4ms/STS/hardware/Kicad-6-project/TrigSampler.kicad_sch

## KiCad design hardware/Kicad-6-project/TrigSampler.kicad_sch (2021-11-30)

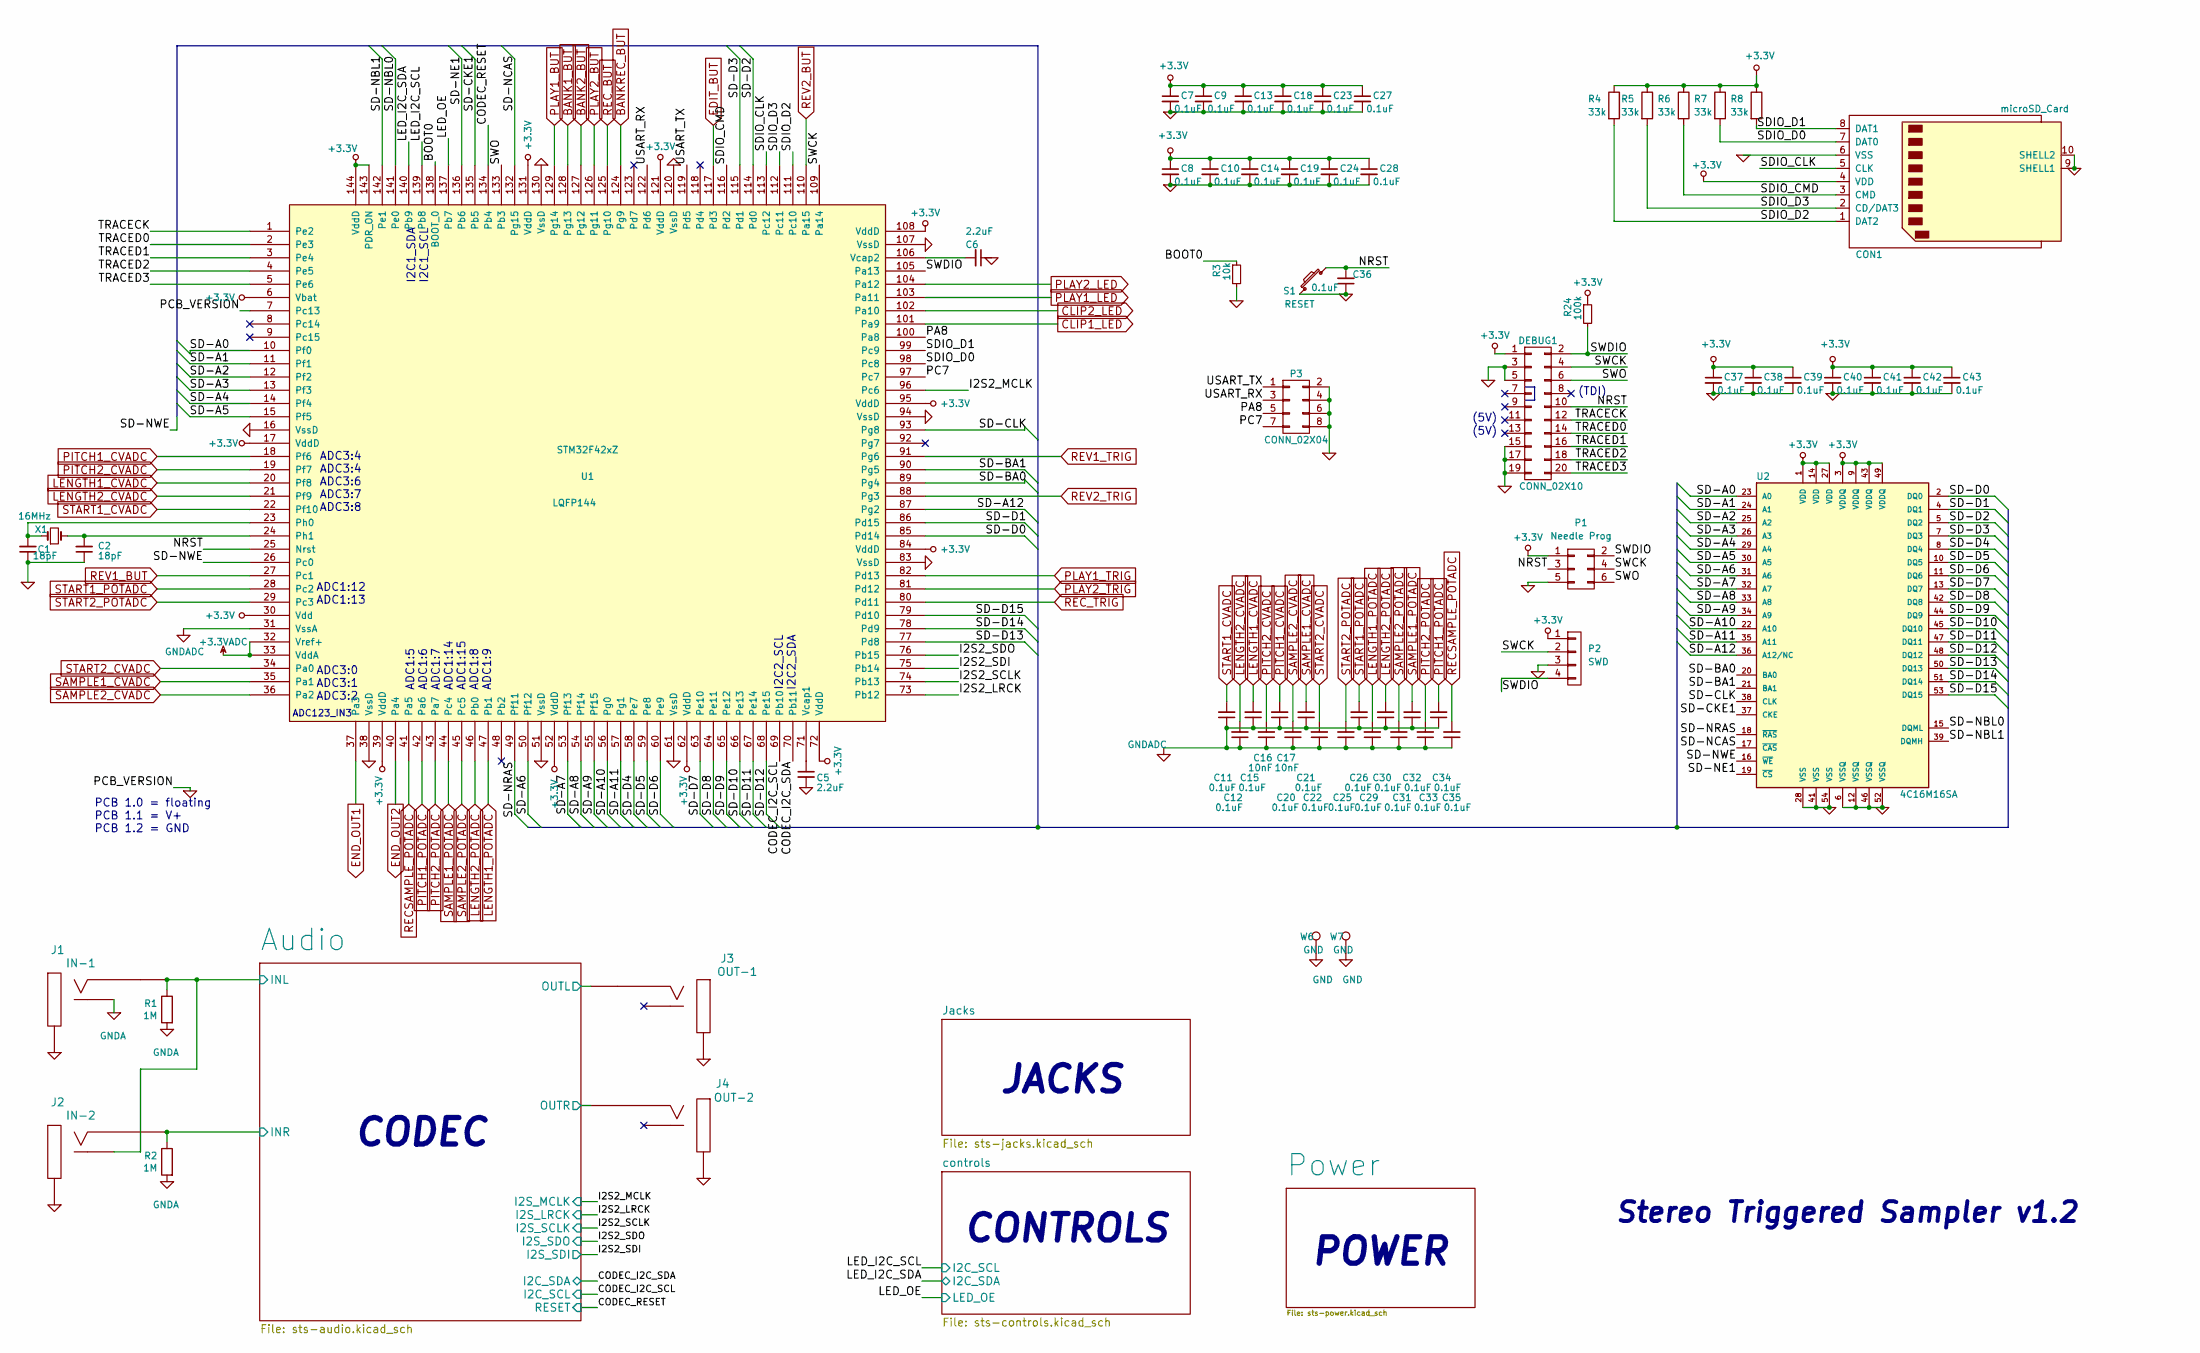
[picture p6: schematic TrigSampler.kicad_sch]

Parts:
C1, C2: 18pF; C0603
C5, C6: 2.2uF; C0603
C7, C8, C9, C10, C11, C12, C13, C14, C15, C18, C19, C20, C21, C22, C23, C24, C25, C26, C27, C28, C29, C30, C31, C32, C33, C34, C35, C36, C37, C38, C39, C40, C41, C42, C43: 0.1uF; C0603
C16, C17: 10nF; C0603
CON1: microSD_Card; MICROSD-YAMAICHI-PJS-VERT
DEBUG1: CONN_02X10; CONN-2x10-SMT-127
J1: IN-1; PJ301M-12
J2: IN-2; PJ301M-12
J3: OUT-1; PJ301M-12
J4: OUT-2; PJ301M-12
P1: Needle Prog; J-LINK_6PIN_NEEDLE_ADAPTER
P2: SWD; Pin_Header_Straight_1x04_Pitch2.54mm
P3: CONN_02X04; Pin_Header_Straight_2x04
R1, R2: 1M; R0603
R3: 10k; R0603
R4, R5, R6, R7, R8: 33k; R0603
R24: 100k; R0603
S1: RESET; BUTTON-TACT-PTS540
U1: STM32F42xZ; LQFP-144_20x20mm_Pitch0.5mm
U2: 4C16M16SA; TSOP-54_W400
W6, W7: GND; TestPoint_Pad_10
X1: 16MHz; FA-238

Connections:
+3.3V: C7.1, C8.1, C9.1, C10.1, C13.1, C14.1, C18.1, C19.1, C23.1, C24.1, C27.1, C28.1, C37.1, C38.1, C39.1, C40.1, C41.1, C42.1, C43.1, CON1.4 (VDD), DEBUG1.1, P1.1, P2.1, R4.1, R5.1, R6.1, R7.1, R8.1, R24.1, U1.6 (Vbat), U1.17 (VddD), U1.30 (Vdd), U1.39 (VddD), U1.52 (VddD), U1.62 (VddD), U1.72 (VddD), U1.84 (VddD), U1.95 (VddD), U1.108 (VddD), U1.121 (VddD), U1.131 (VddD), U1.143 (PDR_ON), U1.144 (VddD), U2.1 (VDD), U2.3 (VDDQ), U2.9 (VDDQ), U2.14 (VDD), U2.27 (VDD), U2.43 (VDDQ), U2.49 (VDDQ)
+3.3VADC: U1.32 (Vref+), U1.33 (VddA)
BANK1_BUT: U1.128 (Pg13)
BANK2_BUT: U1.127 (Pg12)
BANKREC_BUT: U1.124 (Pg9)
BOOT0: R3.1, U1.138 (BOOT_0)
CLIP1_LED: U1.101 (Pa9)
CLIP2_LED: U1.102 (Pa10)
CODEC_I2C_SCL: U1.69 (Pb10)
CODEC_I2C_SDA: U1.70 (Pb11)
CODEC_RESET: U1.134 (Pb4)
EDIT_BUT: U1.117 (Pd3)
END_OUT1: U1.37 (Pa3)
END_OUT2: U1.40 (Pa4)
GND: C1.1, C2.1, C5.2, C6.1, C7.2, C8.2, C9.2, C10.2, C13.2, C14.2, C18.2, C19.2, C23.2, C24.2, C27.2, C28.2, C36.1, C37.2, C38.2, C39.2, C40.2, C41.2, C42.2, C43.2, CON1.6 (VSS), CON1.9 (SHELL1), CON1.10 (SHELL2), DEBUG1.3, DEBUG1.5, DEBUG1.15, DEBUG1.17, DEBUG1.19, J1.2 (SHEILD), J2.2 (SHEILD), J3.2 (SHEILD), J4.2 (SHEILD), P1.5, P2.3, P3.2, P3.4, P3.6, P3.8, R3.2, S1.1, U1.7 (Pc13), U1.16 (VssD), U1.38 (VssD), U1.51 (VssD), U1.61 (VssD), U1.83 (VssD), U1.94 (VssD), U1.107 (VssD), U1.120 (VssD), U1.130 (VssD), U2.6 (VSSQ), U2.12 (VSSQ), U2.28 (VSS), U2.41 (VSS), U2.46 (VSSQ), U2.52 (VSSQ), U2.54 (VSS), W6.1, W7.1
GNDA: J1.3 (SW), R1.2, R2.2
GNDADC: C11.1, C12.1, C15.1, C16.1, C17.1, C20.1, C21.1, C22.1, C25.1, C26.1, C29.1, C30.1, C31.1, C32.1, C33.1, C34.1, C35.1, U1.31 (VssA)
I2S2_LRCK: U1.73 (Pb12)
I2S2_MCLK: U1.96 (Pc6)
I2S2_SCLK: U1.74 (Pb13)
I2S2_SDI: U1.75 (Pb14)
I2S2_SDO: U1.76 (Pb15)
INL: J1.1 (SIG), J2.3 (SW), R1.1
INR: J2.1 (SIG), R2.1
LED_I2C_SCL: U1.139 (Pb8)
LED_I2C_SDA: U1.140 (Pb9)
LED_OE: U1.137 (Pb7)
LENGTH1_CVADC: C15.2, U1.20 (Pf8)
LENGTH1_POTADC: C29.2, U1.47 (Pb1)
LENGTH2_CVADC: C12.2, U1.21 (Pf9)
LENGTH2_POTADC: C30.2, U1.46 (Pb0)
NRST: C36.2, DEBUG1.10, P1.3, S1.2, U1.25 (Nrst)
unnamed: C1.2, U1.23 (Ph0), X1.1
unnamed: C2.2, U1.24 (Ph1), X1.2
unnamed: C5.1, U1.71 (Vcap1)
unnamed: C6.2, U1.106 (Vcap2)
OUTL: J3.1 (SIG)
OUTR: J4.1 (SIG)
PA8: P3.5, U1.100 (Pa8)
PC7: P3.7, U1.97 (Pc7)
PITCH1_CVADC: C17.2, U1.18 (Pf6)
PITCH1_POTADC: C34.2, U1.42 (Pa6)
PITCH2_CVADC: C16.2, U1.19 (Pf7)
PITCH2_POTADC: C33.2, U1.43 (Pa7)
PLAY1_BUT: U1.129 (Pg14)
PLAY1_LED: U1.103 (Pa11)
PLAY1_TRIG: U1.82 (Pd13)
PLAY2_BUT: U1.126 (Pg11)
PLAY2_LED: U1.104 (Pa12)
PLAY2_TRIG: U1.81 (Pd12)
RECSAMPLE_POTADC: C35.2, U1.41 (Pa5)
REC_BUT: U1.125 (Pg10)
REC_TRIG: U1.80 (Pd11)
REV1_BUT: U1.27 (Pc1)
REV1_TRIG: U1.91 (Pg6)
REV2_BUT: U1.110 (Pa15)
REV2_TRIG: U1.88 (Pg3)
SAMPLE1_CVADC: C21.2, U1.35 (Pa1)
SAMPLE1_POTADC: C32.2, U1.44 (Pc4)
SAMPLE2_CVADC: C20.2, U1.36 (Pa2)
SAMPLE2_POTADC: C31.2, U1.45 (Pc5)
SD-A0: U1.10 (Pf0), U2.23 (A0)
SD-A1: U1.11 (Pf1), U2.24 (A1)
SD-A2: U1.12 (Pf2), U2.25 (A2)
SD-A3: U1.13 (Pf3), U2.26 (A3)
SD-A4: U1.14 (Pf4), U2.29 (A4)
SD-A5: U1.15 (Pf5), U2.30 (A5)
SD-A6: U1.50 (Pf12), U2.31 (A6)
SD-A7: U1.53 (Pf13), U2.32 (A7)
SD-A8: U1.54 (Pf14), U2.33 (A8)
SD-A9: U1.55 (Pf15), U2.34 (A9)
SD-A10: U1.56 (Pg0), U2.22 (A10)
SD-A11: U1.57 (Pg1), U2.35 (A11)
SD-A12: U1.87 (Pg2), U2.36 (A12/NC)
SD-BA0: U1.89 (Pg4), U2.20 (BA0)
SD-BA1: U1.90 (Pg5), U2.21 (BA1)
SD-CKE1: U1.135 (Pb5), U2.37 (CKE)
SD-CLK: U1.93 (Pg8), U2.38 (CLK)
SD-D0: U1.85 (Pd14), U2.2 (DQ0)
SD-D1: U1.86 (Pd15), U2.4 (DQ1)
SD-D2: U1.114 (Pd0), U2.5 (DQ2)
SD-D3: U1.115 (Pd1), U2.7 (DQ3)
SD-D4: U1.58 (Pe7), U2.8 (DQ4)
SD-D5: U1.59 (Pe8), U2.10 (DQ5)
SD-D6: U1.60 (Pe9), U2.11 (DQ6)
SD-D7: U1.63 (Pe10), U2.13 (DQ7)
SD-D8: U1.64 (Pe11), U2.42 (DQ8)
SD-D9: U1.65 (Pe12), U2.44 (DQ9)
SD-D10: U1.66 (Pe13), U2.45 (DQ10)
SD-D11: U1.67 (Pe14), U2.47 (DQ11)
SD-D12: U1.68 (Pe15), U2.48 (DQ12)
SD-D13: U1.77 (Pd8), U2.50 (DQ13)
SD-D14: U1.78 (Pd9), U2.51 (DQ14)
SD-D15: U1.79 (Pd10), U2.53 (DQ15)
SD-NBL0: U1.141 (Pe0), U2.15 (DQML)
SD-NBL1: U1.142 (Pe1), U2.39 (DQMH)
SD-NCAS: U1.132 (Pg15), U2.17 (~CAS)
SD-NE1: U1.136 (Pb6), U2.19 (~CS)
SD-NRAS: U1.49 (Pf11), U2.18 (~RAS)
SD-NWE: U1.26 (Pc0), U2.16 (~WE)
SDIO_CLK: CON1.5 (CLK), U1.113 (Pc12)
SDIO_CMD: CON1.3 (CMD), R6.2, U1.116 (Pd2)
SDIO_D0: CON1.7 (DAT0), R7.2, U1.98 (Pc8)
SDIO_D1: CON1.8 (DAT1), R8.2, U1.99 (Pc9)
SDIO_D2: CON1.1 (DAT2), R4.2, U1.111 (Pc10)
SDIO_D3: CON1.2 (CD/DAT3), R5.2, U1.112 (Pc11)
START1_CVADC: C11.2, U1.22 (Pf10)
START1_POTADC: C26.2, U1.28 (Pc2)
START2_CVADC: C22.2, U1.34 (Pa0)
START2_POTADC: C25.2, U1.29 (Pc3)
SWCK: DEBUG1.4, P1.4, P2.2, U1.109 (Pa14)
SWDIO: DEBUG1.2, P1.2, P2.4, R24.2, U1.105 (Pa13)
SWO: DEBUG1.6, P1.6, U1.133 (Pb3)
TRACECK: DEBUG1.12, U1.1 (Pe2)
TRACED0: DEBUG1.14, U1.2 (Pe3)
TRACED1: DEBUG1.16, U1.3 (Pe4)
TRACED2: DEBUG1.18, U1.4 (Pe5)
TRACED3: DEBUG1.20, U1.5 (Pe6)
USART_RX: P3.3, U1.122 (Pd6)
USART_TX: P3.1, U1.119 (Pd5)

Notes on the sheet:
JACKS
PCB 1.0 = floating PCB 1.1 = V+ PCB 1.2 = GND
(5V)
ADC3:4 ADC3:4 ADC3:6 ADC3:7 ADC3:8
ADC123_IN3
ADC1:5 ADC1:6 ADC1:7 ADC1:14 ADC1:15 ADC1:8 ADC1:9
ADC1:12 ADC1:13
POWER
I2C1_SDA I2C1_SCL
(TDI)
I2C2_SCL I2C2_SDA
Stereo Triggered Sampler v1.2
CONTROLS
CODEC
ADC3:0 ADC3:1 ADC3:2
