4ms/STS/hardware/Kicad-6-project/sts-audio.kicad_sch

## KiCad design hardware/Kicad-6-project/sts-audio.kicad_sch (2021-11-30)

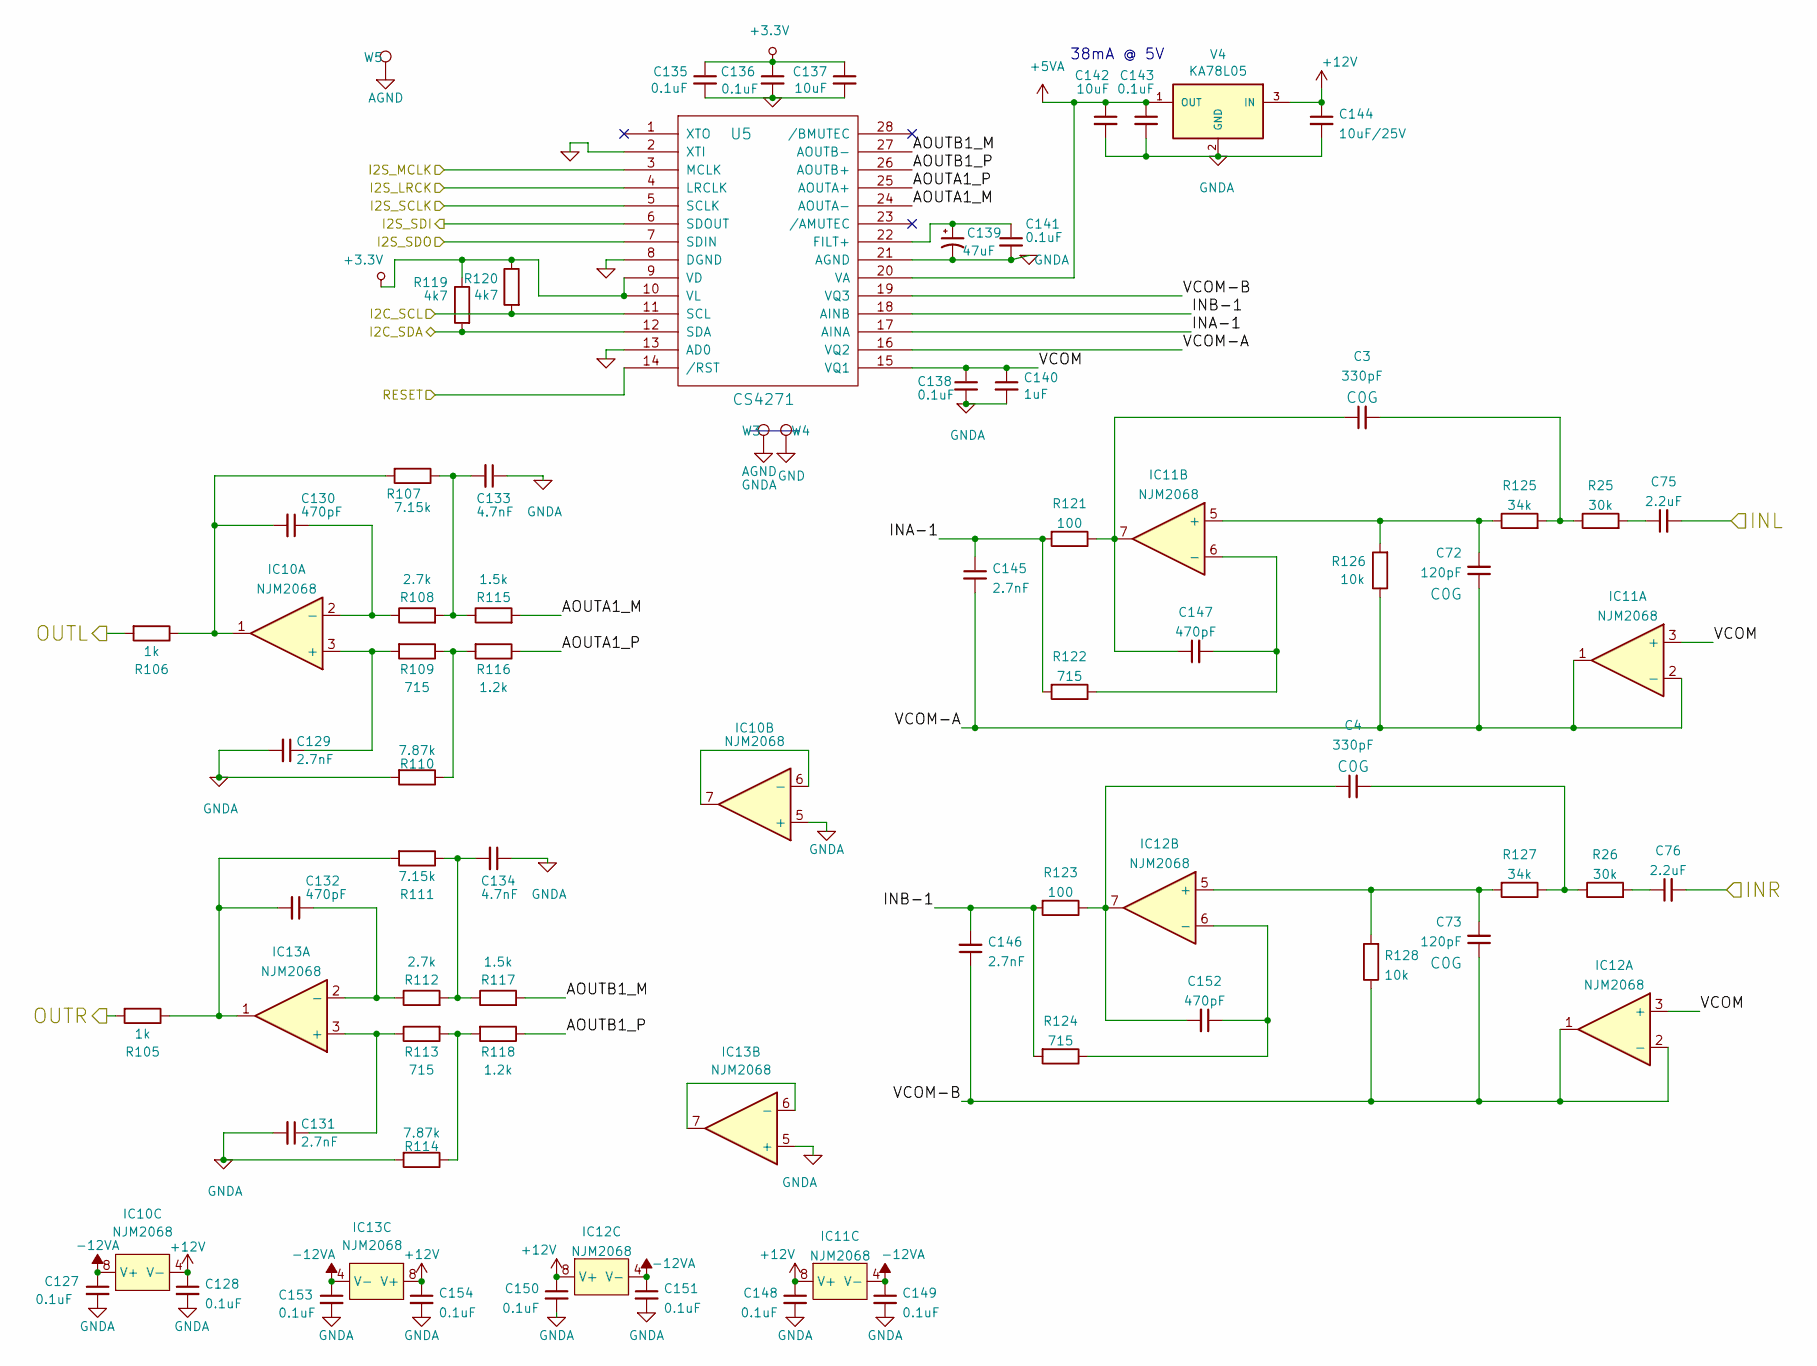
[picture p7: schematic sts-audio.kicad_sch]

Parts:
C3, C4: 330pF; C0603; Tolerance 1%
C72, C73: 120pF; C0603; Tolerance 1%
C75, C76: 2.2uF; C0603
C127, C128, C135, C136, C138, C141, C143, C148, C149, C150, C151, C153, C154: 0.1uF; C0603
C129, C131, C145, C146: 2.7nF; C0603
C130, C132, C147, C152: 470pF; C0603
C133, C134: 4.7nF; C0603
C137, C142: 10uF; C0603
C139: 47uF; c_elec_5x5.3
C140: 1uF; C0603
C144: 10uF/25V; C1206
IC10, IC11, IC12, IC13: NJM2068; TSSOP-8_4.4x3mm_Pitch0.65mm; Part Number NJM2068V-TE1
R25, R26: 30k; R0603
R105, R106: 1k; R0603
R107, R111: 7.15k; R0603
R108, R112: 2.7k; R0603
R109, R113, R122, R124: 715; R0603
R110, R114: 7.87k; R0603
R115, R117: 1.5k; R0603
R116, R118: 1.2k; R0603
R119, R120: 4k7; R0603
R121, R123: 100; R0603
R125, R127: 34k; R0603
R126, R128: 10k; R0603
U5: CS4271; TSSOP-28_4.4x9.7mm_Pitch0.65mm
V4: KA78L05; SOT89-3_Housing
W3, W5: AGND; PAD-06
W4: GND; PAD-06

Connections:
+3.3V: C135.1, C136.1, C137.1, R119.1, R120.1, U5.9 (VD), U5.10 (VL)
+5VA: C142.1, C143.1, U5.20 (VA), V4.1 (OUT)
+12V: C128.1, C144.1, C148.1, C150.1, C154.1, IC10.4 (V-), IC11.8 (V+), IC12.8 (V+), IC13.8 (V+), V4.3 (IN)
-12VA: C127.1, C149.1, C151.1, C153.1, IC10.8 (V+), IC11.4 (V-), IC12.4 (V-), IC13.4 (V-)
AOUTA1_M: R115.2, U5.24 (AOUTA-)
AOUTA1_P: R116.1, U5.25 (AOUTA+)
AOUTB1_M: R117.2, U5.27 (AOUTB-)
AOUTB1_P: R118.1, U5.26 (AOUTB+)
GND: C135.2, C136.2, C137.2, U5.2 (XTI), U5.8 (DGND), U5.13 (AD0), W4.1, W5.1
GNDA: C127.2, C128.2, C129.2, C131.2, C133.1, C134.1, C138.2, C139.2, C140.2, C141.2, C142.2, C143.2, C144.2, C148.2, C149.2, C150.2, C151.2, C153.2, C154.2, IC10.5 (+), IC13.5 (+), R110.2, R114.2, U5.21 (AGND), V4.2 (GND), W3.1
I2C_SCL: R120.2, U5.11 (SCL)
I2C_SDA: R119.2, U5.12 (SDA)
I2S_LRCK: U5.4 (LRCLK)
I2S_MCLK: U5.3 (MCLK)
I2S_SCLK: U5.5 (SCLK)
I2S_SDI: U5.6 (SDOUT)
I2S_SDO: U5.7 (SDIN)
INA-1: C145.1, R121.2, R122.2, U5.17 (AINA)
INB-1: C146.2, R123.2, R124.2, U5.18 (AINB)
INL: C75.2
INR: C76.2
unnamed: C3.2, R25.1, R125.2
unnamed: C4.2, R26.1, R127.1
unnamed: C72.2, IC11.5 (+), R125.1, R126.2
unnamed: C73.2, IC12.5 (+), R127.2, R128.2
unnamed: C75.1, R25.2
unnamed: C76.1, R26.2
unnamed: C129.1, IC10.3 (+), R109.2
unnamed: C130.1, IC10.2 (-), R108.1
unnamed: C130.2, IC10.1, R106.1, R107.2
unnamed: C131.1, IC13.3 (+), R113.1
unnamed: C132.1, IC13.2 (-), R112.1
unnamed: C132.2, IC13.1, R105.1, R111.2
unnamed: C133.2, R107.1, R108.2, R115.1
unnamed: C134.2, R111.1, R112.2, R117.1
unnamed: C139.1, C141.1, U5.22 (FILT+)
unnamed: C3.1, C147.1, IC11.7, R121.1
unnamed: C147.2, IC11.6 (-), R122.1
unnamed: C152.1, IC12.6 (-), R124.1
unnamed: C4.1, C152.2, IC12.7, R123.1
unnamed: IC10.6 (-), IC10.7
unnamed: IC13.6 (-), IC13.7
unnamed: R109.1, R110.1, R116.2
unnamed: R113.2, R114.1, R118.2
OUTL: R106.2
OUTR: R105.2
RESET: U5.14 (/RST)
VCOM: C138.1, C140.1, IC11.3 (+), IC12.3 (+), U5.15 (VQ1)
VCOM-A: C72.1, C145.2, IC11.1, IC11.2 (-), R126.1, U5.16 (VQ2)
VCOM-B: C73.1, C146.1, IC12.1, IC12.2 (-), R128.1, U5.19 (VQ3)

Notes on the sheet:
38mA @ 5V
