4ms/STS/hardware/Kicad-6-project/sts-controls.kicad_sch

## KiCad design hardware/Kicad-6-project/sts-controls.kicad_sch (2021-11-30)

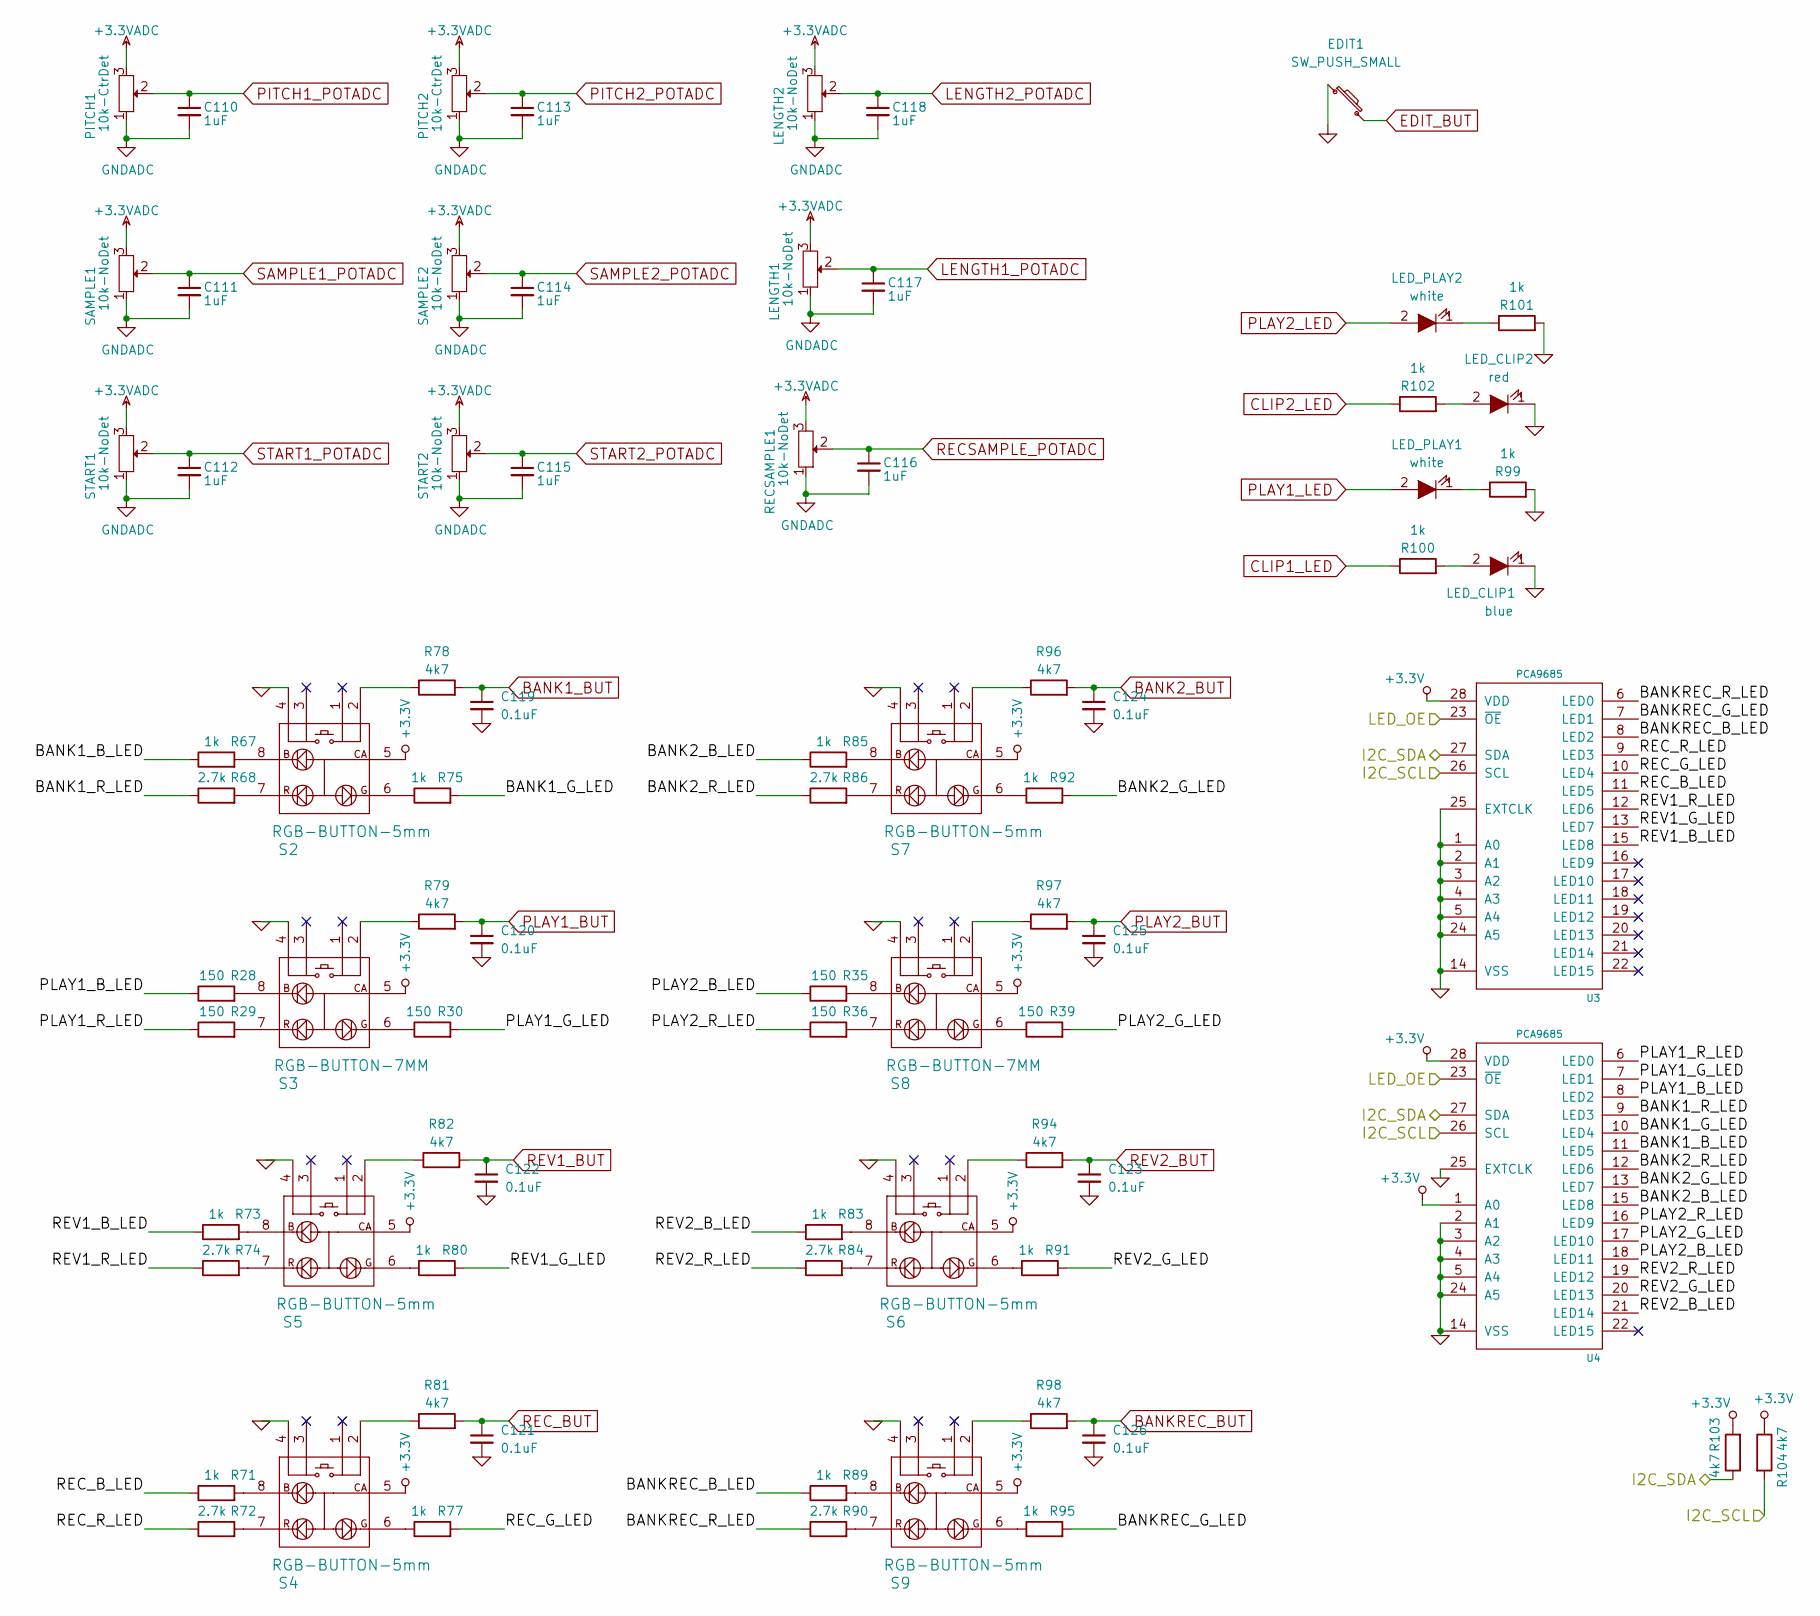
[picture p8: schematic sts-controls.kicad_sch]

Parts:
C110, C111, C112, C113, C114, C115, C116, C117, C118: 1uF; C0603
C119, C120, C121, C122, C123, C124, C125, C126: 0.1uF; C0603
EDIT1: SW_PUSH_SMALL; SPST-SUB
LED_CLIP1: blue; LED-3MM-SQUARE-ANODE
LED_CLIP2: red; LED-3MM-SQUARE-ANODE
LED_PLAY1, LED_PLAY2: white; LED-3MM-SQUARE-ANODE
LENGTH1, LENGTH2: 10k-NoDet; 16MM-RV16AF-4A-NODET
PITCH1, PITCH2: 10k-CtrDet; 16MM-RV16AF-4A-CTRDET
R28, R29, R30, R35, R36, R39: 150; R0603
R67, R71, R73, R75, R77, R80, R83, R85, R89, R91, R92, R95, R99, R100, R101, R102: 1k; R0603
R68, R72, R74, R84, R86, R90: 2.7k; R0603
R78, R79, R81, R82, R94, R96, R97, R98, R103, R104: 4k7; R0603
RECSAMPLE1: 10k-NoDet; 16MM-RV16AF-4A-NODET
S2, S7: RGB-BUTTON-5mm; Button_RgbLED_SPST_TC002
S3, S8: RGB-BUTTON-7MM; Button_RgbLED_SPST_PB615303HL-7mm
S4, S5, S6, S9: RGB-BUTTON-5mm; RGB-SPST-LED-TC002
SAMPLE1, SAMPLE2: 10k-NoDet; 16MM-RV16AF-4A-NODET
START1, START2: 10k-NoDet; 16MM-RV16AF-4A-NODET
U3, U4: PCA9685; TSSOP-28_4.4x9.7mm_Pitch0.65mm

Connections:
+3.3V: R103.2, R104.1, S2.5 (CA), S3.5 (CA), S4.5 (CA), S5.5 (CA), S6.5 (CA), S7.5 (CA), S8.5 (CA), S9.5 (CA), U3.28 (VDD), U4.1 (A0), U4.28 (VDD)
+3.3VADC: LENGTH1.3, LENGTH2.3, PITCH1.3, PITCH2.3, RECSAMPLE1.3, SAMPLE1.3, SAMPLE2.3, START1.3, START2.3
BANK1_BUT: C119.1, R78.2
BANK1_B_LED: R67.1, U4.11 (LED5)
BANK1_G_LED: R75.2, U4.10 (LED4)
BANK1_R_LED: R68.1, U4.9 (LED3)
BANK2_BUT: C124.1, R96.2
BANK2_B_LED: R85.1, U4.15 (LED8)
BANK2_G_LED: R92.2, U4.13 (LED7)
BANK2_R_LED: R86.1, U4.12 (LED6)
BANKREC_BUT: C126.1, R98.2
BANKREC_B_LED: R89.1, U3.8 (LED2)
BANKREC_G_LED: R95.2, U3.7 (LED1)
BANKREC_R_LED: R90.1, U3.6 (LED0)
CLIP1_LED: R100.1
CLIP2_LED: R102.1
EDIT_BUT: EDIT1.2
GND: C119.2, C120.2, C121.2, C122.2, C123.2, C124.2, C125.2, C126.2, EDIT1.1, LED_CLIP1.1 (K), LED_CLIP2.1 (K), R99.2, R101.2, S2.4 (UP-B), S3.4 (UP-B), S4.4 (UP-B), S5.4 (UP-B), S6.4 (UP-B), S7.4 (UP-B), S8.4 (UP-B), S9.4 (UP-B), U3.1 (A0), U3.2 (A1), U3.3 (A2), U3.4 (A3), U3.5 (A4), U3.14 (VSS), U3.24 (A5), U3.25 (EXTCLK), U4.2 (A1), U4.3 (A2), U4.4 (A3), U4.5 (A4), U4.14 (VSS), U4.24 (A5), U4.25 (EXTCLK)
GNDADC: C110.2, C111.2, C112.2, C113.2, C114.2, C115.2, C116.2, C117.2, C118.2, LENGTH1.1, LENGTH2.1, PITCH1.1, PITCH2.1, RECSAMPLE1.1, SAMPLE1.1, SAMPLE2.1, START1.1, START2.1
I2C_SCL: R104.2, U3.26 (SCL), U4.26 (SCL)
I2C_SDA: R103.1, U3.27 (SDA), U4.27 (SDA)
LED_OE: U3.23 (~OE), U4.23 (~OE)
LENGTH1_POTADC: C117.1, LENGTH1.2
LENGTH2_POTADC: C118.1, LENGTH2.2
unnamed: LED_CLIP1.2 (A), R100.2
unnamed: LED_CLIP2.2 (A), R102.2
unnamed: LED_PLAY1.1 (K), R99.1
unnamed: LED_PLAY2.1 (K), R101.1
unnamed: R28.2, S3.8 (B)
unnamed: R29.2, S3.7 (R)
unnamed: R30.1, S3.6 (G)
unnamed: R35.2, S8.8 (B)
unnamed: R36.2, S8.7 (R)
unnamed: R39.1, S8.6 (G)
unnamed: R67.2, S2.8 (B)
unnamed: R68.2, S2.7 (R)
unnamed: R71.2, S4.8 (B)
unnamed: R72.2, S4.7 (R)
unnamed: R73.2, S5.8 (B)
unnamed: R74.2, S5.7 (R)
unnamed: R75.1, S2.6 (G)
unnamed: R77.1, S4.6 (G)
unnamed: R78.1, S2.2 (POLE-A)
unnamed: R79.1, S3.2 (POLE-A)
unnamed: R80.1, S5.6 (G)
unnamed: R81.1, S4.2 (POLE-A)
unnamed: R82.1, S5.2 (POLE-A)
unnamed: R83.2, S6.8 (B)
unnamed: R84.2, S6.7 (R)
unnamed: R85.2, S7.8 (B)
unnamed: R86.2, S7.7 (R)
unnamed: R89.2, S9.8 (B)
unnamed: R90.2, S9.7 (R)
unnamed: R91.1, S6.6 (G)
unnamed: R92.1, S7.6 (G)
unnamed: R94.1, S6.2 (POLE-A)
unnamed: R95.1, S9.6 (G)
unnamed: R96.1, S7.2 (POLE-A)
unnamed: R97.1, S8.2 (POLE-A)
unnamed: R98.1, S9.2 (POLE-A)
PITCH1_POTADC: C110.1, PITCH1.2
PITCH2_POTADC: C113.1, PITCH2.2
PLAY1_BUT: C120.1, R79.2
PLAY1_B_LED: R28.1, U4.8 (LED2)
PLAY1_G_LED: R30.2, U4.7 (LED1)
PLAY1_LED: LED_PLAY1.2 (A)
PLAY1_R_LED: R29.1, U4.6 (LED0)
PLAY2_BUT: C125.1, R97.2
PLAY2_B_LED: R35.1, U4.18 (LED11)
PLAY2_G_LED: R39.2, U4.17 (LED10)
PLAY2_LED: LED_PLAY2.2 (A)
PLAY2_R_LED: R36.1, U4.16 (LED9)
RECSAMPLE_POTADC: C116.1, RECSAMPLE1.2
REC_BUT: C121.1, R81.2
REC_B_LED: R71.1, U3.11 (LED5)
REC_G_LED: R77.2, U3.10 (LED4)
REC_R_LED: R72.1, U3.9 (LED3)
REV1_BUT: C122.1, R82.2
REV1_B_LED: R73.1, U3.15 (LED8)
REV1_G_LED: R80.2, U3.13 (LED7)
REV1_R_LED: R74.1, U3.12 (LED6)
REV2_BUT: C123.1, R94.2
REV2_B_LED: R83.1, U4.21 (LED14)
REV2_G_LED: R91.2, U4.20 (LED13)
REV2_R_LED: R84.1, U4.19 (LED12)
SAMPLE1_POTADC: C111.1, SAMPLE1.2
SAMPLE2_POTADC: C114.1, SAMPLE2.2
START1_POTADC: C112.1, START1.2
START2_POTADC: C115.1, START2.2
