4ms/STS/hardware/Kicad-6-project/sts-jacks.kicad_sch

## KiCad design hardware/Kicad-6-project/sts-jacks.kicad_sch (2021-11-30)

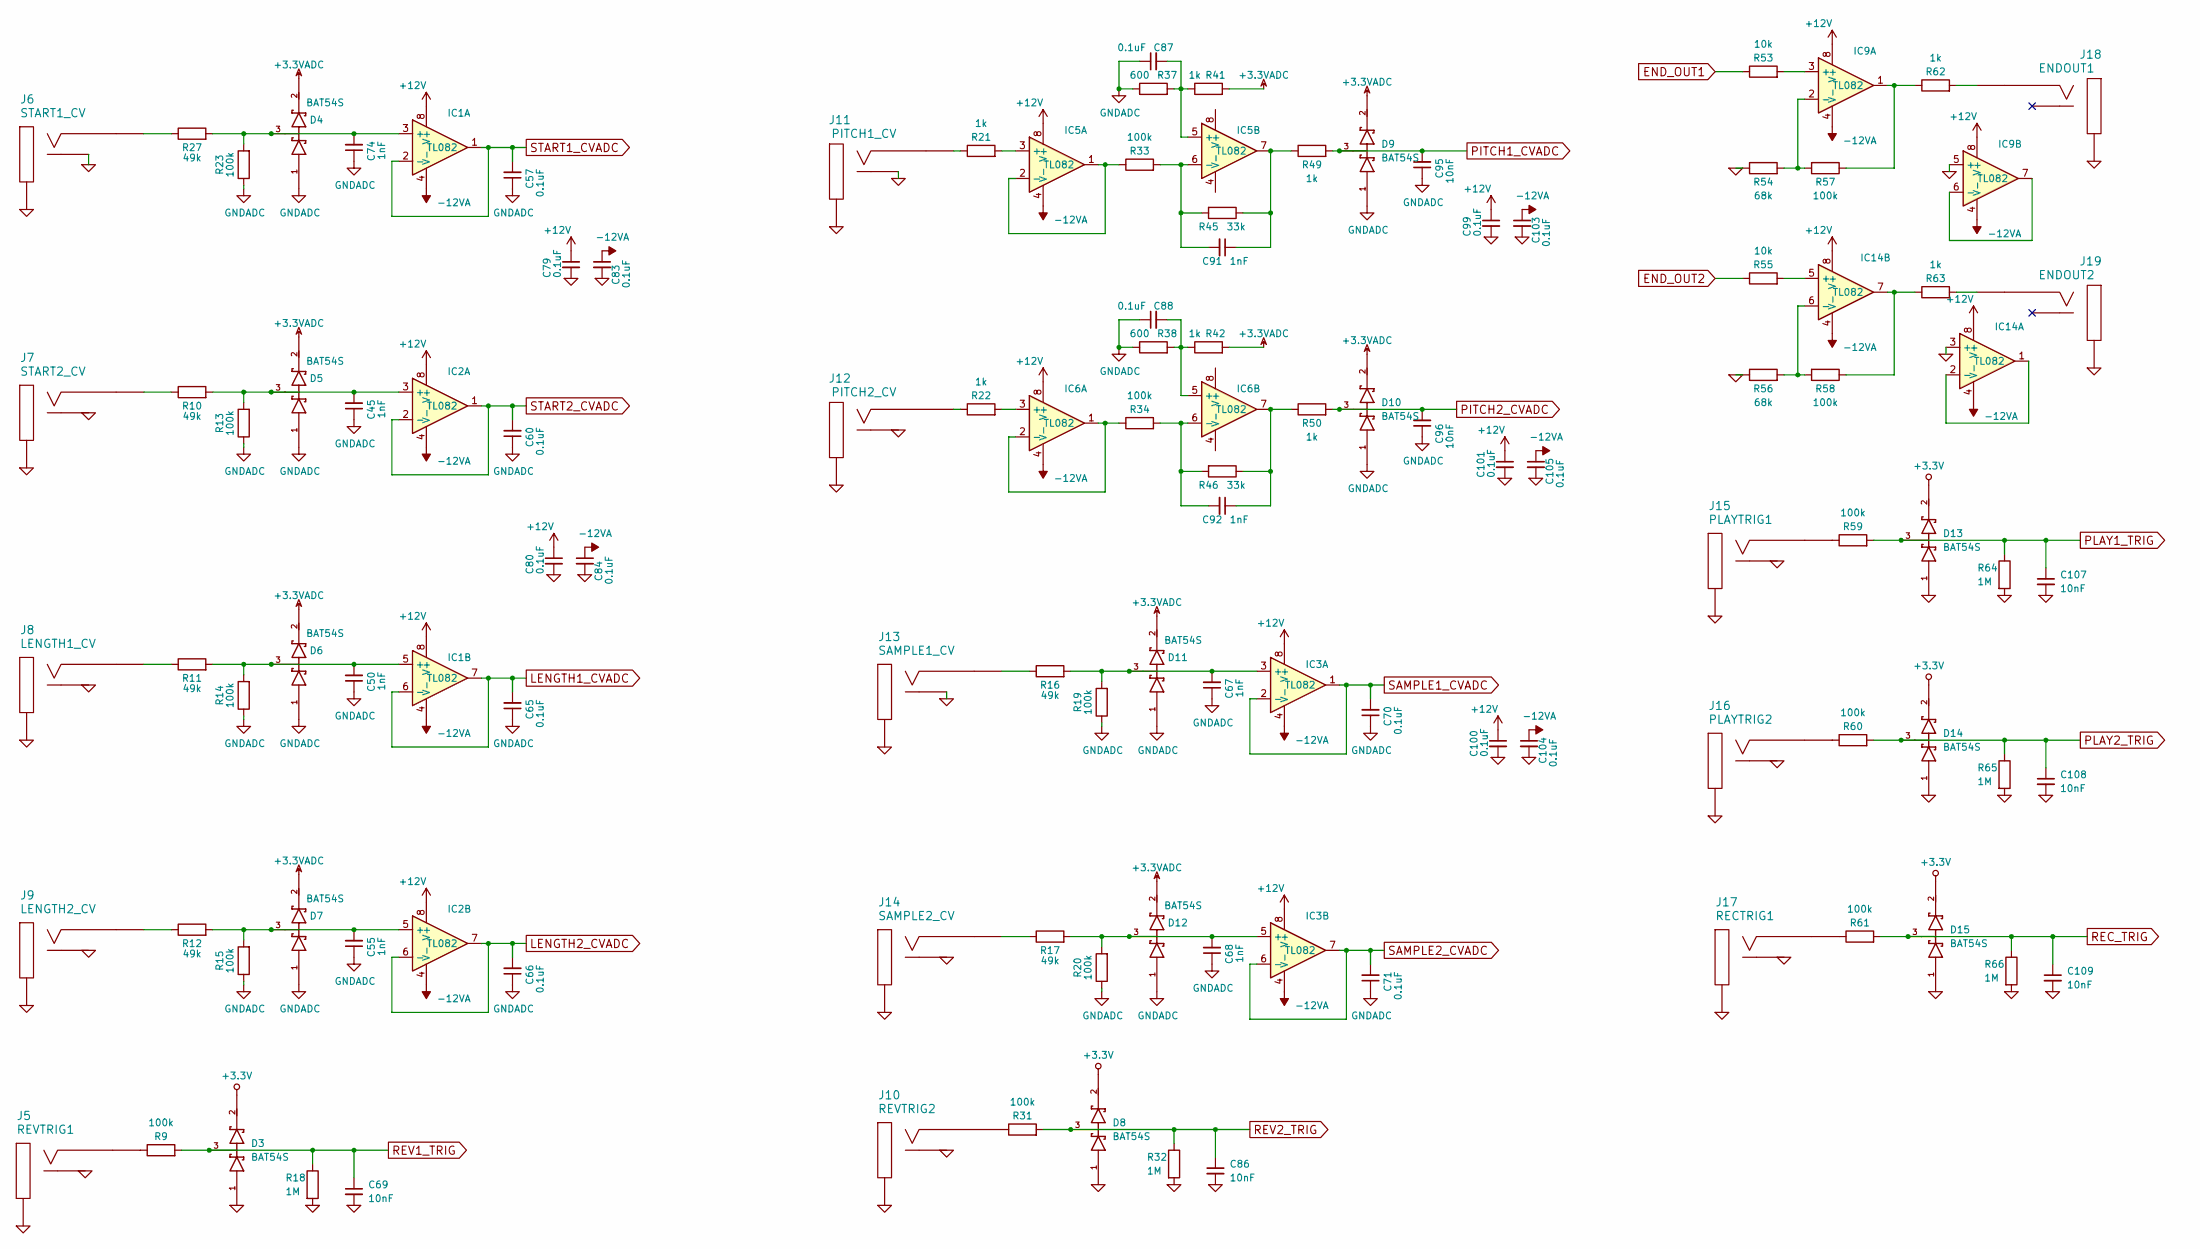
[picture p9: schematic sts-jacks.kicad_sch]

Parts:
C45, C50, C55, C67, C68, C74, C91, C92: 1nF; C0603
C57, C60, C65, C66, C70, C71, C79, C80, C83, C84, C87, C88, C99, C100, C101, C103, C104, C105: 0.1uF; C0603
C69, C86, C95, C96, C107, C108, C109: 10nF; C0603
D3, D4, D5, D6, D7, D8, D9, D10, D11, D12, D13, D14, D15: BAT54S; SOT23
IC1, IC2, IC3, IC5, IC6, IC9, IC14: TL082; TSSOP-8_4.4x3mm_Pitch0.65mm
J5: REVTRIG1; PJ301M-12
J6: START1_CV; PJ301M-12
J7: START2_CV; PJ301M-12
J8: LENGTH1_CV; PJ301M-12
J9: LENGTH2_CV; PJ301M-12
J10: REVTRIG2; PJ301M-12
J11: PITCH1_CV; PJ301M-12
J12: PITCH2_CV; PJ301M-12
J13: SAMPLE1_CV; PJ301M-12
J14: SAMPLE2_CV; PJ301M-12
J15: PLAYTRIG1; PJ301M-12
J16: PLAYTRIG2; PJ301M-12
J17: RECTRIG1; PJ301M-12
J18: ENDOUT1; PJ301M-12
J19: ENDOUT2; PJ301M-12
R9, R13, R14, R15, R19, R20, R23, R31, R33, R34, R57, R58, R59, R60, R61: 100k; R0603
R10, R11, R12, R16, R17, R27: 49k; R0603
R18, R32, R64, R65, R66: 1M; R0603
R21, R22, R41, R42, R49, R50, R62, R63: 1k; R0603
R37, R38: 600; R0603
R45, R46: 33k; R0603
R53, R55: 10k; R0603
R54, R56: 68k; R0603

Connections:
+3.3V: D3.2 (cathode), D8.2 (cathode), D13.2 (cathode), D14.2 (cathode), D15.2 (cathode)
+3.3VADC: D4.2 (cathode), D5.2 (cathode), D6.2 (cathode), D7.2 (cathode), D9.2 (cathode), D10.2 (cathode), D11.2 (cathode), D12.2 (cathode), R41.2, R42.2
+12V: C79.1, C80.1, C99.1, C100.1, C101.1, IC1.8 (V+), IC2.8 (V+), IC3.8 (V+), IC5.8 (V+), IC6.8 (V+), IC9.8 (V+), IC14.8 (V+)
-12VA: C83.1, C84.1, C103.1, C104.1, C105.1, IC1.4 (V-), IC2.4 (V-), IC3.4 (V-), IC5.4 (V-), IC6.4 (V-), IC9.4 (V-), IC14.4 (V-)
END_OUT1: R53.1
END_OUT2: R55.1
GND: C69.2, C79.2, C80.2, C83.2, C84.2, C86.2, C99.2, C100.2, C101.2, C103.2, C104.2, C105.2, C107.2, C108.2, C109.2, D3.1 (Anode), D8.1 (Anode), D13.1 (Anode), D14.1 (Anode), D15.1 (Anode), IC9.5 (+), IC14.3 (+), J5.2 (SHEILD), J5.3 (SW), J6.2 (SHEILD), J6.3 (SW), J7.2 (SHEILD), J7.3 (SW), J8.2 (SHEILD), J8.3 (SW), J9.2 (SHEILD), J9.3 (SW), J10.2 (SHEILD), J10.3 (SW), J11.2 (SHEILD), J11.3 (SW), J12.2 (SHEILD), J12.3 (SW), J13.2 (SHEILD), J13.3 (SW), J14.2 (SHEILD), J14.3 (SW), J15.2 (SHEILD), J15.3 (SW), J16.2 (SHEILD), J16.3 (SW), J17.2 (SHEILD), J17.3 (SW), J18.2 (SHEILD), J19.2 (SHEILD), R18.2, R32.2, R54.1, R56.1, R64.2, R65.2, R66.2
GNDADC: C45.1, C50.1, C55.1, C57.1, C60.1, C65.1, C66.1, C67.1, C68.1, C70.1, C71.1, C74.1, C87.1, C88.1, C95.1, C96.1, D4.1 (Anode), D5.1 (Anode), D6.1 (Anode), D7.1 (Anode), D9.1 (Anode), D10.1 (Anode), D11.1 (Anode), D12.1 (Anode), R13.1, R14.1, R15.1, R19.1, R20.1, R23.1, R37.1, R38.1
LENGTH1_CVADC: C65.2, IC1.6 (-), IC1.7
LENGTH2_CVADC: C66.2, IC2.6 (-), IC2.7
unnamed: C45.2, D5.3 (AK), IC2.3 (+), R10.2, R13.2
unnamed: C50.2, D6.3 (AK), IC1.5 (+), R11.2, R14.2
unnamed: C55.2, D7.3 (AK), IC2.5 (+), R12.2, R15.2
unnamed: C67.2, D11.3 (AK), IC3.3 (+), R16.2, R19.2
unnamed: C68.2, D12.3 (AK), IC3.5 (+), R17.2, R20.2
unnamed: C74.2, D4.3 (AK), IC1.3 (+), R23.2, R27.2
unnamed: C87.2, IC5.5 (+), R37.2, R41.1
unnamed: C88.2, IC6.5 (+), R38.2, R42.1
unnamed: C91.1, IC5.7, R45.1, R49.1
unnamed: C91.2, IC5.6 (-), R33.2, R45.2
unnamed: C92.1, IC6.7, R46.1, R50.1
unnamed: C92.2, IC6.6 (-), R34.2, R46.2
unnamed: IC5.1, IC5.2 (-), R33.1
unnamed: IC5.3 (+), R21.2
unnamed: IC6.1, IC6.2 (-), R34.1
unnamed: IC6.3 (+), R22.2
unnamed: IC9.1, R57.1, R62.1
unnamed: IC9.2 (-), R54.2, R57.2
unnamed: IC9.3 (+), R53.2
unnamed: IC9.6 (-), IC9.7
unnamed: IC14.1, IC14.2 (-)
unnamed: IC14.5 (+), R55.2
unnamed: IC14.6 (-), R56.2, R58.2
unnamed: IC14.7, R58.1, R63.1
unnamed: J5.1 (SIG), R9.1
unnamed: J6.1 (SIG), R27.1
unnamed: J7.1 (SIG), R10.1
unnamed: J8.1 (SIG), R11.1
unnamed: J9.1 (SIG), R12.1
unnamed: J10.1 (SIG), R31.1
unnamed: J11.1 (SIG), R21.1
unnamed: J12.1 (SIG), R22.1
unnamed: J13.1 (SIG), R16.1
unnamed: J14.1 (SIG), R17.1
unnamed: J15.1 (SIG), R59.1
unnamed: J16.1 (SIG), R60.1
unnamed: J17.1 (SIG), R61.1
unnamed: J18.1 (SIG), R62.2
unnamed: J19.1 (SIG), R63.2
PITCH1_CVADC: C95.2, D9.3 (AK), R49.2
PITCH2_CVADC: C96.2, D10.3 (AK), R50.2
PLAY1_TRIG: C107.1, D13.3 (AK), R59.2, R64.1
PLAY2_TRIG: C108.1, D14.3 (AK), R60.2, R65.1
REC_TRIG: C109.1, D15.3 (AK), R61.2, R66.1
REV1_TRIG: C69.1, D3.3 (AK), R9.2, R18.1
REV2_TRIG: C86.1, D8.3 (AK), R31.2, R32.1
SAMPLE1_CVADC: C70.2, IC3.1, IC3.2 (-)
SAMPLE2_CVADC: C71.2, IC3.6 (-), IC3.7
START1_CVADC: C57.2, IC1.1, IC1.2 (-)
START2_CVADC: C60.2, IC2.1, IC2.2 (-)
