4ms/STS/hardware/Kicad-6-project/sts-power.kicad_sch

## KiCad design hardware/Kicad-6-project/sts-power.kicad_sch (2021-11-30)

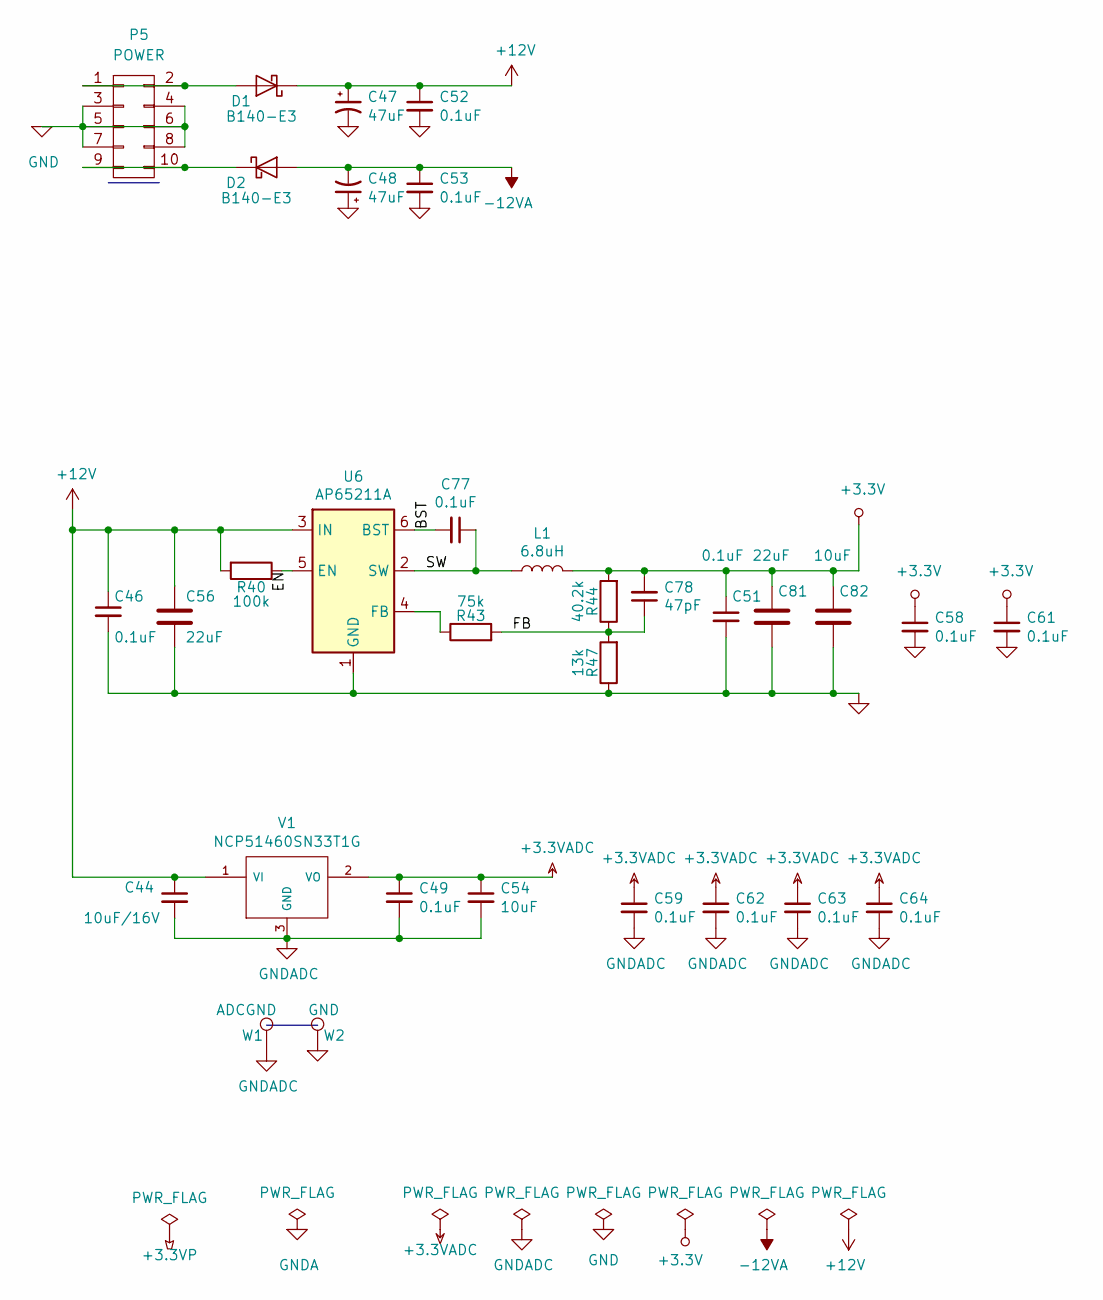
[picture p10: schematic sts-power.kicad_sch]

Parts:
C44: 10uF/16V; C0805
C46, C49, C51, C52, C53, C58, C59, C61, C62, C63, C64: 0.1uF; C0603
C47, C48: 47uF; c_elec_5x5.3
C54: 10uF; C0603
C56: 22uF; C_1206; Part number TMK316BBJ226ML-T
C77: 0.1uF; C_0603
C78: 47pF; C_0603; Part number 885012005078
C81: 22uF; C_0805; Part number JMK212ABJ226MD-T
C82: 10uF; C_0603
D1, D2: B140-E3; SMA_Standard
L1: 6.8uH; L_Taiyo-Yuden_NR-40xx; Part number NRS4018T6R8MDGJ
P5: POWER; Header_2x05_Pitch2.54mm_TH_-12v_Label
R40: 100k; R_0603
R43: 75k; R_0603
R44: 40.2k; R_0603
R47: 13k; R_0603
U6: AP65211A; TSOT-23-6
V1: NCP51460SN33T1G; SOT23-3_PO132
W1: ADCGND; PAD-06
W2: GND; PAD-06

Connections:
+3.3V: C51.1, C58.1, C61.1, C78.2, C81.1, C82.1, L1.2, R44.2
+3.3VADC: C49.1, C54.1, C59.1, C62.1, C63.1, C64.1, V1.2 (VO)
+12V: C44.1, C46.1, C47.1, C52.1, C56.1, D1.1 (K), R40.2, U6.3 (IN), V1.1 (VI)
-12VA: C48.2, C53.1, D2.2 (A)
BST: C77.2, U6.6 (BST)
EN: R40.1, U6.5 (EN)
FB: C78.1, R43.2, R44.1, R47.2
GND: C46.2, C47.2, C48.1, C51.2, C52.2, C53.2, C56.2, C58.2, C61.2, C81.2, C82.2, P5.3, P5.4, P5.5, P5.6, P5.7, P5.8, R47.1, U6.1 (GND), W2.1
GNDADC: C44.2, C49.2, C54.2, C59.2, C62.2, C63.2, C64.2, V1.3 (GND), W1.1
unnamed: D1.2 (A), P5.1, P5.2
unnamed: D2.1 (K), P5.9, P5.10
unnamed: R43.1, U6.4 (FB)
SW: C77.1, L1.1, U6.2 (SW)
