4ms/STS/calcs/voltoct/voltoct.h

const float voltoct[4096]={
32.43788481032838,	//0
32.38282319245161,	//1
32.3278550387998,	//2
32.27298019072231,	//3
32.21819848983779,	//4
32.16350977803373,	//5
32.10891389746602,	//6
32.05441069055848,	//7
32.0000000000024,	//8
31.9456816687561,	//9
31.89145554004447,	//10
31.83732145735851,	//11
31.7832792644549,	//12
31.72932880535552,	//13
31.67546992434702,	//14
31.62170246598037,	//15
31.56802627507041,	//16
31.51444119669538,	//17
31.4609470761965,	//18
31.40754375917753,	//19
31.3542310915043,	//20
31.30100891930426,	//21
31.24787708896607,	//22
31.19483544713914,	//23
31.14188384073315,	//24
31.0890221169177,	//25
31.03625012312176,	//26
30.9835677070333,	//27
30.93097471659884,	//28
30.878471000023,	//29
30.82605640576805,	//30
30.77373078255351,	//31
30.72149397935566,	//32
30.66934584540717,	//33
30.6172862301966,	//34
30.56531498346803,	//35
30.51343195522055,	//36
30.4616369957079,	//37
30.40992995543798,	//38
30.35831068517248,	//39
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
};
