4ms/STS/src/user_settings.c

/*
 * user_settings.c - handles user settings stored on SD Card
 *
 * Author: Dan Green (danngreen1@gmail.com)
 *
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
 * See http://creativecommons.org/licenses/MIT/ for more information.
 *
 * -----------------------------------------------------------------------------
 */

#include "user_settings.h"
#include "dig_pins.h"
#include "globals.h"
#include "params.h"
#include "str_util.h"
#include "sts_filesystem.h"

extern uint8_t global_mode[NUM_GLOBAL_MODES];

extern GlobalParams global_params;

//
//WIP: standardized structure for user settings
//
// #define MAX_SETTINGS_CHOICES 3
// #define	SETTING_INTEGER 255

// typedef struct UserSettings{
// 	char	setting_text[40];						// Text for block header in settings file
// 	uint8_t	num_choices;							// Number of choices. Must be: 2 <= num_choices < MAX_SETTINGS_CHOICES, or num_choices == SETTING_INTEGER
// 													// If num_choices == SETTING_INTEGER, then the value is a int32_t and value_choice[] and text_choice[] are ignored
// 	char	text_choice[MAX_SETTINGS_CHOICES][12];	// Text for the choices
// 	int32_t	value_choice[MAX_SETTINGS_CHOICES];		// Values to set global_mode[ gm_index ]
// 	uint8_t	gm_index;								// which global_mode[] is associated
// } UserSettings;

void set_default_user_settings(void) {
	global_mode[STEREO_MODE] = 0;
	global_mode[REC_24BITS] = 0;
	global_mode[AUTO_STOP_ON_SAMPLE_CHANGE] = AutoStop_OFF;
	global_mode[LENGTH_FULL_START_STOP] = 0;

	global_mode[QUANTIZE_CH1] = 0;
	global_mode[QUANTIZE_CH2] = 0;

	global_mode[PERC_ENVELOPE] = 1;
	global_mode[FADEUPDOWN_ENVELOPE] = 1;

	global_mode[STARTUPBANK_CH1] = 0;
	global_mode[STARTUPBANK_CH2] = 0;

	global_mode[TRIG_DELAY] = 8;

	global_params.fade_time_ms = 24;

	global_params.auto_inc_slot_num_after_rec_trig = 0;
}

FRESULT save_user_settings(void) {
	FRESULT res;
	char filepath[_MAX_LFN];
	FIL settings_file;

	// Check sys_dir is ok
	res = check_sys_dir();
	if (res == FR_OK) {
		// Create/overwrite the settings file
		str_cat(filepath, SYS_DIR_SLASH, SETTINGS_FILE);
		res = f_open(&settings_file, filepath, FA_CREATE_ALWAYS | FA_WRITE);
		if (res != FR_OK)
			return (res);

		//Write the header
		f_printf(&settings_file, "##\n");
		f_printf(&settings_file, "## 4ms Stereo Triggered Sampler\n");
		f_printf(&settings_file, "## Settings File\n");
		f_printf(&settings_file, "## http://www.4mscompany.com/sts.php\n");
		f_printf(&settings_file, "##\n");
		f_printf(&settings_file, "## [STEREO MODE] can be \"stereo\" or \"mono\" (default)\n");
		f_printf(&settings_file, "## [RECORD SAMPLE BITS] can be 24 or 16 (default)\n");
#ifdef ENABLE_VARIABLE_RECORD_SAMPLE_RATE
		f_printf(&settings_file, "## [RECORD SAMPLE RATE] can be 96k, 88.2k, 48k, or 44.1k (default)\n");
#endif
		f_printf(&settings_file,
				 "## [AUTO STOP ON SAMPLE CHANGE] can be \"No\", \"Looping Only\" or \"Yes\" (default)\n");
		f_printf(&settings_file, "## [PLAY BUTTON STOPS WITH LENGTH AT FULL] can be \"No\" or \"Yes\" (default)\n");
		f_printf(&settings_file, "## [QUANTIZE CHANNEL 1 1V/OCT JACK] can be \"Yes\" or \"No\" (default)\n");
		f_printf(&settings_file, "## [QUANTIZE CHANNEL 2 1V/OCT JACK] can be \"Yes\" or \"No\" (default)\n");
		f_printf(&settings_file, "## [SHORT SAMPLE PERCUSSIVE ENVELOPE] can be \"No\" or \"Yes\" (default)\n");
		f_printf(&settings_file, "## [CROSSFADE SAMPLE END POINTS] can be \"No\" or \"Yes\" (default)\n");
		f_printf(
			&settings_file,
			"## [STARTUP BANK CHANNEL 1] can be a number between 0 and 59 (default is 0, which is the White bank)\n");
		f_printf(
			&settings_file,
			"## [STARTUP BANK CHANNEL 2] can be a number between 0 and 59 (default is 0, which is the White bank)\n");
		f_printf(&settings_file,
				 "## [TRIG DELAY] can be a number between 1 and 10 which translates to a delay between 0.5ms and 20ms, "
				 "respectively (default is 5)\n");
		f_printf(&settings_file,
				 "## [FADE TIME] can be a number between 0 and 255 which sets the fade in/out time in milliseconds. "
				 "(0 is actually 0.36ms, and 255 is 255ms. Default is 24)\n");
		f_printf(&settings_file, "## [AUTO INCREMENT REC SLOT ON TRIG] can be \"Yes\" or \"No\" (default)\n");
		f_printf(&settings_file, "##\n");
		f_printf(&settings_file, "## Deleting this file will restore default settings\n");
		f_printf(&settings_file, "##\n\n");

		// Write the stereo mode setting
		f_printf(&settings_file, "[STEREO MODE]\n");

		if (global_mode[STEREO_MODE])
			f_printf(&settings_file, "stereo\n\n");
		else
			f_printf(&settings_file, "mono\n\n");

		// Write the 24bit record mode setting
		f_printf(&settings_file, "[RECORD SAMPLE BITS]\n");

		if (global_mode[REC_24BITS])
			f_printf(&settings_file, "24\n\n");
		else
			f_printf(&settings_file, "16\n\n");

#ifdef ENABLE_VARIABLE_RECORD_SAMPLE_RATE
		// Write the record sample rate setting
		f_printf(&settings_file, "[RECORD SAMPLE RATE]\n");

		if (global_params.record_sample_rate == REC_48K)
			f_printf(&settings_file, "48k\n\n");
		else if (global_params.record_sample_rate == REC_88K)
			f_printf(&settings_file, "88.2k\n\n");
		else if (global_params.record_sample_rate == REC_96K)
			f_printf(&settings_file, "96k\n\n");
		else
			f_printf(&settings_file, "44.1k\n\n");
#endif

		// Write the Auto Stop on Sample Change mode setting
		f_printf(&settings_file, "[AUTO STOP ON SAMPLE CHANGE]\n");

		if (global_mode[AUTO_STOP_ON_SAMPLE_CHANGE] == AutoStop_ALWAYS)
			f_printf(&settings_file, "Yes\n\n");
		else if (global_mode[AUTO_STOP_ON_SAMPLE_CHANGE] == AutoStop_OFF)
			f_printf(&settings_file, "No\n\n");
		else if (global_mode[AUTO_STOP_ON_SAMPLE_CHANGE] == AutoStop_LOOPING)
			f_printf(&settings_file, "Looping Only\n\n");

		// Write the Auto Stop on Sample Change mode setting
		f_printf(&settings_file, "[PLAY BUTTON STOPS WITH LENGTH AT FULL]\n");

		if (global_mode[LENGTH_FULL_START_STOP])
			f_printf(&settings_file, "Yes\n\n");
		else
			f_printf(&settings_file, "No\n\n");

		// Write the Quantize Channel 1 setting
		f_printf(&settings_file, "[QUANTIZE CHANNEL 1 1V/OCT JACK]\n");

		if (global_mode[QUANTIZE_CH1])
			f_printf(&settings_file, "Yes\n\n");
		else
			f_printf(&settings_file, "No\n\n");

		// Write the Quantize Channel 2 setting
		f_printf(&settings_file, "[QUANTIZE CHANNEL 2 1V/OCT JACK]\n");

		if (global_mode[QUANTIZE_CH2])
			f_printf(&settings_file, "Yes\n\n");
		else
			f_printf(&settings_file, "No\n\n");

		// Write the Perc Envelope setting
		f_printf(&settings_file, "[SHORT SAMPLE PERCUSSIVE ENVELOPE]\n");

		if (global_mode[PERC_ENVELOPE])
			f_printf(&settings_file, "Yes\n\n");
		else
			f_printf(&settings_file, "No\n\n");

		// Write the Fade Up/Down Envelope setting
		f_printf(&settings_file, "[CROSSFADE SAMPLE END POINTS]\n");

		if (global_mode[FADEUPDOWN_ENVELOPE])
			f_printf(&settings_file, "Yes\n\n");
		else
			f_printf(&settings_file, "No\n\n");

		// Write the Channel 1 startup bank setting
		f_printf(&settings_file, "[STARTUP BANK CHANNEL 1]\n");
		f_printf(&settings_file, "%d\n\n", global_mode[STARTUPBANK_CH1]);

		// Write the Channel 2 startup bank setting
		f_printf(&settings_file, "[STARTUP BANK CHANNEL 2]\n");
		f_printf(&settings_file, "%d\n\n", global_mode[STARTUPBANK_CH2]);

		// Write the Trig Delay setting
		f_printf(&settings_file, "[TRIG DELAY]\n");
		f_printf(&settings_file, "%d\n\n", global_mode[TRIG_DELAY]);

		// Write the Trig Delay setting
		f_printf(&settings_file, "[FADE TIME]\n");
		f_printf(&settings_file, "%d\n\n", global_params.fade_time_ms);

		// Write Auto Inc Rec Slot setting
		f_printf(&settings_file, "[AUTO INCREMENT REC SLOT ON TRIG]\n");
		f_printf(&settings_file, "%s\n\n", global_params.auto_inc_slot_num_after_rec_trig ? "Yes" : "No");

		res = f_close(&settings_file);
	}

	return (res);
}

FRESULT read_user_settings(void) {
	FRESULT res;
	char filepath[_MAX_LFN];
	char read_buffer[255];
	FIL settings_file;
	uint8_t cur_setting_found;

	// Check sys_dir is ok
	res = check_sys_dir();
	if (res == FR_OK) {
		// Open the settings file read-only
		str_cat(filepath, SYS_DIR_SLASH, SETTINGS_FILE);
		res = f_open(&settings_file, filepath, FA_READ);
		if (res != FR_OK)
			return (res);

		cur_setting_found = NoSetting;
		while (!f_eof(&settings_file)) {
			// Read next line
			if (f_gets(read_buffer, 255, &settings_file) == 0)
				return (FR_INT_ERR);

			// Ignore lines starting with #
			if (read_buffer[0] == '#')
				continue;

			// Ignore blank lines
			if (read_buffer[0] == 0)
				continue;

			// Remove /n from buffer
			read_buffer[str_len(read_buffer) - 1] = 0;

			// Look for a settings section header
			if (read_buffer[0] == '[') {
				if (str_startswith_nocase(read_buffer, "[STEREO MODE]")) {
					cur_setting_found = StereoMode; //stereo mode section detected
					continue;
				}

				if (str_startswith_nocase(read_buffer, "[RECORD SAMPLE BITS]")) {
					cur_setting_found = RecordSampleBits; //24bit recording mode section detected
					continue;
				}

				if (str_startswith_nocase(read_buffer, "[RECORD SAMPLE RATE")) {
					cur_setting_found = RecordSampleRate; //Sample rate section detected
					continue;
				}

				if (str_startswith_nocase(read_buffer, "[AUTO STOP ON SAMPLE CHANGE]")) {
					cur_setting_found = AutoStopSampleChange; //Auto Stop Mode section detected
					continue;
				}

				if (str_startswith_nocase(read_buffer, "[PLAY BUTTON STOPS WITH LENGTH AT FULL]")) {
					cur_setting_found = PlayStopsLengthFull;
					continue;
				}
				if (str_startswith_nocase(read_buffer, "[QUANTIZE CHANNEL 1")) {
					cur_setting_found = QuantizeChannel1;
					continue;
				}
				if (str_startswith_nocase(read_buffer, "[QUANTIZE CHANNEL 2")) {
					cur_setting_found = QuantizeChannel2;
					continue;
				}
				if (str_startswith_nocase(read_buffer, "[SHORT SAMPLE PERCUSSIVE ENVELOPE")) {
					cur_setting_found = PercEnvelope;
					continue;
				}
				if (str_startswith_nocase(read_buffer, "[CROSSFADE SAMPLE END POINTS")) {
					cur_setting_found = FadeEnvelope;
					continue;
				}
				if (str_startswith_nocase(read_buffer, "[STARTUP BANK CHANNEL 1")) {
					cur_setting_found = StartUpBank_ch1;
					continue;
				}
				if (str_startswith_nocase(read_buffer, "[STARTUP BANK CHANNEL 2")) {
					cur_setting_found = StartUpBank_ch2;
					continue;
				}
				if (str_startswith_nocase(read_buffer, "[TRIG DELAY")) {
					cur_setting_found = TrigDelay;
					continue;
				}

				if (str_startswith_nocase(read_buffer, "[FADE TIME")) {
					cur_setting_found = FadeUpDownTime;
					continue;
				}

				if (str_startswith_nocase(read_buffer, "[AUTO INCREMENT REC SLOT ON TRIG")) {
					cur_setting_found = AutoIncRecSlot;
					continue;
				}
			}

			//Look for setting values

			if (cur_setting_found == StereoMode) {
				if (str_startswith_nocase(read_buffer, "stereo"))
					global_mode[STEREO_MODE] = 1;
				else if (str_startswith_nocase(read_buffer, "mono"))
					global_mode[STEREO_MODE] = 0;

				cur_setting_found = NoSetting; //back to looking for headers
			}

			if (cur_setting_found == RecordSampleBits) {
				if (str_startswith_nocase(read_buffer, "24"))
					global_mode[REC_24BITS] = 1;
				else
					//if (str_startswith_nocase(read_buffer, "16"))
					global_mode[REC_24BITS] = 0;

				cur_setting_found = NoSetting; //back to looking for headers
			}

#ifdef ENABLE_VARIABLE_RECORD_SAMPLE_RATE
			if (cur_setting_found == RecordSampleRate) {
				if (str_startswith_nocase(read_buffer, "48"))
					global_params.record_sample_rate = REC_48K;
				else if (str_startswith_nocase(read_buffer, "88"))
					global_params.record_sample_rate = REC_88K;
				else if (str_startswith_nocase(read_buffer, "96"))
					global_params.record_sample_rate = REC_96K;
				else
					global_params.record_sample_rate = REC_44K;

				cur_setting_found = NoSetting; //back to looking for headers
			}
#endif

			if (cur_setting_found == AutoStopSampleChange) {
				if (str_startswith_nocase(read_buffer, "Yes"))
					global_mode[AUTO_STOP_ON_SAMPLE_CHANGE] = AutoStop_ALWAYS;
				else if (str_startswith_nocase(read_buffer, "Looping Only"))
					global_mode[AUTO_STOP_ON_SAMPLE_CHANGE] = AutoStop_LOOPING;
				else
					global_mode[AUTO_STOP_ON_SAMPLE_CHANGE] = AutoStop_OFF;

				cur_setting_found = NoSetting; //back to looking for headers
			}

			if (cur_setting_found == PlayStopsLengthFull) {
				if (str_startswith_nocase(read_buffer, "Yes"))
					global_mode[LENGTH_FULL_START_STOP] = 1;
				else
					global_mode[LENGTH_FULL_START_STOP] = 0;

				cur_setting_found = NoSetting; //back to looking for headers
			}

			if (cur_setting_found == QuantizeChannel1) {
				if (str_startswith_nocase(read_buffer, "Yes"))
					global_mode[QUANTIZE_CH1] = 1;
				else
					global_mode[QUANTIZE_CH1] = 0;

				cur_setting_found = NoSetting; //back to looking for headers
			}

			if (cur_setting_found == QuantizeChannel2) {
				if (str_startswith_nocase(read_buffer, "Yes"))
					global_mode[QUANTIZE_CH2] = 1;
				else
					global_mode[QUANTIZE_CH2] = 0;

				cur_setting_found = NoSetting; //back to looking for headers
			}

			if (cur_setting_found == PercEnvelope) {
				if (str_startswith_nocase(read_buffer, "Yes"))
					global_mode[PERC_ENVELOPE] = 1;
				else
					global_mode[PERC_ENVELOPE] = 0;

				cur_setting_found = NoSetting; //back to looking for headers
			}

			if (cur_setting_found == FadeEnvelope) {
				if (str_startswith_nocase(read_buffer, "Yes"))
					global_mode[FADEUPDOWN_ENVELOPE] = 1;
				else
					global_mode[FADEUPDOWN_ENVELOPE] = 0;

				cur_setting_found = NoSetting; //back to looking for headers
			}

			if (cur_setting_found == StartUpBank_ch1) {
				global_mode[STARTUPBANK_CH1] = str_xt_int(read_buffer);

				cur_setting_found = NoSetting; //back to looking for headers
			}
			if (cur_setting_found == StartUpBank_ch2) {
				global_mode[STARTUPBANK_CH2] = str_xt_int(read_buffer);

				cur_setting_found = NoSetting; //back to looking for headers
			}

			if (cur_setting_found == TrigDelay) {
				global_mode[TRIG_DELAY] = str_xt_int(read_buffer);
				if (global_mode[TRIG_DELAY] < 1 || global_mode[TRIG_DELAY] > 20)
					global_mode[TRIG_DELAY] = 8;

				cur_setting_found = NoSetting; //back to looking for headers
			}

			if (cur_setting_found == FadeUpDownTime) {
				global_params.fade_time_ms = str_xt_int(read_buffer);
				if (global_params.fade_time_ms < 0 || global_params.fade_time_ms > 255)
					global_params.fade_time_ms = 24;

				cur_setting_found = NoSetting; //back to looking for headers
			}

			if (cur_setting_found == AutoIncRecSlot) {
				global_params.auto_inc_slot_num_after_rec_trig = (str_startswith_nocase(read_buffer, "Yes")) ? 1 : 0;

				cur_setting_found = NoSetting; //back to looking for headers
			}
		}

		res = f_close(&settings_file);
	}
	return (res);
}
