4ms/STS/src/bank.c

/*
 * banks.c - bank functions (naming, enabling, and more)
 *
 * Author: Dan Green (danngreen1@gmail.com)
 *
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
 * See http://creativecommons.org/licenses/MIT/ for more information.
 *
 * -----------------------------------------------------------------------------
 */

#include "bank.h"
#include "dig_pins.h"
#include "globals.h"
#include "params.h"
#include "sample_file.h"
#include "str_util.h"
#include "sts_filesystem.h"

extern uint8_t i_param[NUM_ALL_CHAN][NUM_I_PARAMS];
extern uint8_t flags[NUM_FLAGS];

extern Sample samples[MAX_NUM_BANKS][NUM_SAMPLES_PER_BANK];

extern uint8_t global_mode[NUM_GLOBAL_MODES];

uint8_t bank_status[MAX_NUM_BANKS];

//
// Moving banks
//

void copy_bank(Sample *dst, Sample *src) {
	uint8_t *p_dst;
	uint8_t *p_src;
	uint32_t i;

	p_dst = (uint8_t *)(dst);
	p_src = (uint8_t *)(src);
	for (i = 0; i < (sizeof(Sample) * NUM_SAMPLES_PER_BANK); i++)
		*p_dst++ = *p_src++;
}

//
// Copy bank+40 to bank+50, bank+30 to bank+40, etc...
// The goal is to open up the given bank so we can place a new set of files in there
// FixMe: This must be changed manually if MAX_NUM_BANKS changes
//
void bump_down_banks(uint8_t bank) {
	uint8_t t_bank;

	if (bank < 10) {
		copy_bank(samples[bank + 50], samples[bank + 40]);
		bank_status[bank + 50] = bank_status[bank + 40];
	}

	if (bank < 20) {
		copy_bank(samples[bank + 40], samples[bank + 30]);
		bank_status[bank + 40] = bank_status[bank + 30];
	}

	if (bank < 30) {
		copy_bank(samples[bank + 30], samples[bank + 20]);
		bank_status[bank + 30] = bank_status[bank + 20];
	}

	if (bank < 40) {
		copy_bank(samples[bank + 20], samples[bank + 10]);
		bank_status[bank + 20] = bank_status[bank + 10];
	}

	if (bank < 50) {
		copy_bank(samples[bank + 10], samples[bank]);
		bank_status[bank + 10] = bank_status[bank];
	}

	else
	{ //bank>=50 would get bumped out, so try to place it elsewhere
		t_bank = prev_disabled_bank(MAX_NUM_BANKS);
		copy_bank(samples[t_bank], samples[bank]);
		bank_status[t_bank] = bank_status[bank];
	}
}

///
/// Searching banks
///

//
// Returns the "predominant" path of the samples in a bank
// Todo: make go through all samples in the bank, and set path to the most common path
// For now, it sets path to the path of the first non-empty slot
// Returns 1 if path is set
// Returns 0 if no slots are filled
//
uint8_t get_bank_path(uint8_t bank, char *path) {
	uint8_t samplenum;
	char tmp_path[_MAX_LFN + 1];
	char tmp_filename[_MAX_LFN + 1];
	//	char path_candidates[NUM_SAMPLES_PER_BANK][_MAX_LFN+1];
	//	uint8_t candidate_occurances[NUM_SAMPLES_PER_BANK];
	//	uint8_t candidate_i = 0, path_is_new;

	for (samplenum = 0; samplenum < NUM_SAMPLES_PER_BANK; samplenum++) {
		if (samples[bank][samplenum].filename[0]) {
			if (str_split(samples[bank][samplenum].filename, '/', path, tmp_filename) == 0)
				path[0] = '\0'; //no slashes exist in filename, so path is the root dir

			// Todo untested code:
			// path_is_new = 1;
			// for (i=0;i<candidate_i;i++)
			// {
			// 	if (str_cmp(path_candidates[i], path))
			// 	{
			// 		candidate_occurances[i]++;
			// 		path_is_new = 0;
			// 		break;
			// 	}
			// }
			// if (path_is_new)
			// {
			// 	str_cpy(path_candidates[candidate_i], path); //add it to the candidate array
			// 	candidate_occurances[candidate_i] = 0;
			// 	candidate_i++;
			// }

			return (1); //at least one slot is filled
		}
	}
	path[0] = '\0';
	return (0); //no slots are filled

	// if (!candidate_i)
	// {
	// 	path[0]='\0';
	// 	return(0); //no slots are filled
	// }

	// //Find the top hit
	// top = 0;
	// for (i=0;i<candidate_i;i++)
	// {
	// 	if (candidate_occurances[i] > top)
	// 	{
	// 		top = candidate_occurances[i];
	// 		str_cpy(path, path_candidates[i]);
	// 	}
	// }
	// return(1);
}

//
//Returns the sample number inside the given bank, whose filename matches the given filename
//If not found, returns 0xFF
//
uint8_t find_filename_in_bank(uint8_t bank, char *filename) {
	uint8_t sample;

	if (bank >= MAX_NUM_BANKS)
		return 0xFF; //invalid bank
	if (!is_bank_enabled(bank))
		return 0xFF; //bank not enabled

	for (sample = 0; sample < NUM_SAMPLES_PER_BANK; sample++) {
		if (str_cmp(samples[bank][sample].filename, filename))
			return sample;
	}

	return (0xFF); //not found
}

//Searches all banks for a filename
//Returns bank# if filename exists in ANY sample in that bank
//Returns 0xFF if filename is not found anywhere
//bank is the first bank to look in, setting this to a likely candidate will save CPU time
//
uint8_t find_filename_in_all_banks(uint8_t bank, char *filename) {
	uint8_t orig_bank;

	if (is_bank_enabled(bank))
		orig_bank = bank;
	else
		orig_bank = next_enabled_bank(bank);

	do {
		if (find_filename_in_bank(bank, filename) != 0xFF)
			return (bank);

		bank = next_enabled_bank(bank);
	} while (bank != orig_bank);

	return (0xFF); //not found
}

///
/// Bank naming
///

uint8_t bank_to_color_string(uint8_t bank, char *color) {
	switch (bank) {
		case 0:
			str_cpy(color, "White");
			return (5);
			break;

		case 1:
			str_cpy(color, "Red");
			return (3);
			break;

		case 2:
			str_cpy(color, "Orange");
			return (6);
			break;

		case 3:
			str_cpy(color, "Yellow");
			return (6);
			break;

		case 4:
			str_cpy(color, "Green");
			return (5);
			break;

		case 5:
			str_cpy(color, "Cyan");
			return (4);
			break;

		case 6:
			str_cpy(color, "Blue");
			return (4);
			break;

		case 7:
			str_cpy(color, "Magenta");
			return (7);
			break;

		case 8:
			str_cpy(color, "Lavender");
			return (8);
			break;

		case 9:
			str_cpy(color, "Pearl");
			return (5);
			break;

		default:
			color[0] = 0;
			return (0);
	}
}

// Given a bank number, sets color to the default bank name
// Example: 49 ==> Pearl-4

uint8_t bank_to_color(uint8_t bank, char *color) {
	uint8_t digit1, digit2, len;

	if (bank > 9 && bank < 100) {
		//convert a 2-digit bank number to a color and number

		//First digit: 49 ---> 4
		digit1 = bank / 10;

		//Second digit: 49 ---> (49 - 4*10) = 9
		digit2 = bank - (digit1 * 10);

		//Second digit as a color string i.e. "White" etc
		len = bank_to_color_string(digit2, color);

		//Omit the "0" for the first bank of a color, so "Red-0" is just "Red"
		//Otherwise append a dash and number to the color name
		if (digit1 > 0) {
			//Move pointer to the end of the string (overwrite the \0)
			color += len;

			//Append a dash: "White-"
			*color++ = '-';
			len++;

			//Append first digit as a string: "White-5"
			intToStr(digit1, color, 1);
			len++;
		}

		return (len);
	} else
		return bank_to_color_string(bank, color);
}

// Given a color string, return a bank number.
// If the color string doesn't match any default bank names,
// return MAX_NUM_BANKS
//
uint8_t color_to_bank(char *color) {
	uint8_t i;
	char b_color[11];

	// for every bank number
	for (i = 0; i < MAX_NUM_BANKS; i++) {
		// convert bank number to color
		bank_to_color(i, b_color);

		// compare current bank color with input bank color
		if (str_cmp_nocase(color, b_color)) {
			// ... and return bank number if there's a match
			return (i);
		}
	}
	return (MAX_NUM_BANKS);
}

//
//Given a number, returns the units digit
//This digit refers to the bank color, regardless of blink #
//
uint8_t get_bank_color_digit(uint8_t bank) {
	if (bank < 10)
		return bank;

	while (bank >= 10)
		bank -= 10;
	return (bank);
}

//
//Given a number, returns the tens digit
//This digit refers to the bank blink #, regardless of color
//
uint8_t get_bank_blink_digit(uint8_t bank) {
	return (bank / 10);
}

///
/// Bank Navigation
///

uint8_t next_bank(uint8_t bank) {
	bank++;
	if (bank >= MAX_NUM_BANKS)
		return (0);
	return (bank);
}

// Give a bank number, return the next enabled bank
// If bank==0xFF, return the first enabled bank
//
uint8_t next_enabled_bank(uint8_t bank) {
	uint8_t orig_bank = bank;
	if (orig_bank >= MAX_NUM_BANKS)
		orig_bank = MAX_NUM_BANKS - 1; //otherwise we will have an infinite loop

	do {
		bank++;
		if (bank >= MAX_NUM_BANKS)
			bank = 0;
		if (bank == orig_bank)
			return (0); //no banks are enabled -->> bail out and return the first bank
	} while (!bank_status[bank]);

	return (bank);
}

// Same as next_enabled_bank but acts as if there
// was an enabled bank number 255 (0xFF) after the last bank
//
uint8_t next_enabled_bank_0xFF(uint8_t bank) {
	do {
		bank++;
		if (bank >= MAX_NUM_BANKS)
			return (0xFF);
	} while (!bank_status[bank]);

	return (bank);
}

// Given a bank number, returns the previous enabled bank
// If there are no enabled banks, return 0 (which is the first bank)
//
uint8_t prev_enabled_bank(uint8_t bank) {
	uint8_t orig_bank = bank;
	if (orig_bank >= MAX_NUM_BANKS)
		orig_bank = MAX_NUM_BANKS - 1; //otherwise we will have an infinite loop

	do {
		if (bank == 0)
			bank = MAX_NUM_BANKS - 1;
		else
			bank--;
		if (bank == orig_bank)
			return (0); //no banks are enabled -->> bail out and return the first bank
	} while (!bank_status[bank]);

	return (bank);
}

// Same as prev_enabled_bank but acts as if there
// was an enabled bank number 255 (0xFF) before the first bank
//
uint8_t prev_enabled_bank_0xFF(uint8_t bank) {
	if (bank == 0xFF)
		bank = MAX_NUM_BANKS;
	do {
		if (bank == 0)
			return (0xFF);
		bank -= 1;
	} while (!bank_status[bank]);

	return (bank);
}

// Given a bank number, return the next disabled bank
// If we give bank==0xFF, then return the first disabled bank
//
uint8_t next_disabled_bank(uint8_t bank) {
	uint8_t orig_bank = bank;
	if (orig_bank >= MAX_NUM_BANKS)
		orig_bank = MAX_NUM_BANKS - 1; //otherwise we will have an infinite loop
	do {
		bank++;
		if (bank >= MAX_NUM_BANKS)
			bank = 0;
		if (bank == orig_bank)
			return (0); //no banks are disabled -->> bail out and return the first bank
	} while (bank_status[bank]);

	return (bank);
}

// Given a bank number, return the previous disabled bank
// If we give bank==0xFF, then return the first disabled bank
//
uint8_t prev_disabled_bank(uint8_t bank) {
	uint8_t orig_bank = bank;

	if (bank >= MAX_NUM_BANKS)
		bank = MAX_NUM_BANKS;

	do {
		if (bank == 0)
			bank = MAX_NUM_BANKS;
		bank--;
		if (bank == orig_bank)
			return (bank); //no banks are disabled -->> bail out and return the same bank given
	} while (!bank_status[bank]);

	return (bank);
}

// Go through all banks, and enable/disable each one:
// If the bank has at least one slot with a filename and file_found==1, then enable the bank
// Otherwise disable it
void check_enabled_banks(void) {
	uint32_t sample_num, bank;

	for (bank = 0; bank < MAX_NUM_BANKS; bank++) {
		bank_status[bank] = 0; //does not exist
		for (sample_num = 0; sample_num < NUM_SAMPLES_PER_BANK; sample_num++) {
			if (samples[bank][sample_num].filename[0] != 0 && samples[bank][sample_num].file_found == 1) {
				bank_status[bank] = 1;
				break;
			}
		}
	}
}

uint8_t is_bank_enabled(uint8_t bank) {
	if (bank >= MAX_NUM_BANKS)
		return 0;

	return bank_status[bank] ? 1 : 0;
}

void enable_bank(uint8_t bank) {
	bank_status[bank] = 1;
}
void disable_bank(uint8_t bank) {
	bank_status[bank] = 0;
}

/// Initialization

void init_banks(void) {
	uint32_t first_enabled_bank;
	uint8_t force_reload;

	//Force reloading of banks from disk with button press on boot
	if (REV1BUT && REV2BUT)
		force_reload = 1;
	else
		force_reload = 0;

	load_all_banks(force_reload);

	i_param[0][BANK] = global_mode[STARTUPBANK_CH1];
	i_param[1][BANK] = global_mode[STARTUPBANK_CH2];

	first_enabled_bank = next_enabled_bank(MAX_NUM_BANKS - 1);

	if (!is_bank_enabled(i_param[0][BANK]))
		i_param[0][BANK] = first_enabled_bank;
	if (!is_bank_enabled(i_param[1][BANK]))
		i_param[1][BANK] = first_enabled_bank;

	i_param[2][BANK] =
		next_disabled_bank(first_enabled_bank); //REC bank starts on first disabled bank after the first enabled bank

	flags[PlaySample1Changed] = 1;
	flags[PlaySample2Changed] = 1;
}
